LawrenceK/webbrick/Documentation/WebBrickQuickStart.tex

\documentclass[a4paper,12pt]{article}

\title{\sf{WebBrick}\linebreak Quick Start Guide}

%\lhead{\small{WebBrick Version 6.2 Quick Start Guide}}

\include{Version}

\include{QuickStart}

\printindex

\end{document}
