LawrenceK/webbrick/Documentation/Webrick.tex

\documentclass[a4paper,12pt]{article}

\title{\sf{WebBrick}\linebreak User and Reference Manual}

\include{Version}

\include{Overview}

\include{Architecture}

\include{WebInterface}

\include{Commands}

\include{IoBoard}

\include{Xml}

\include{IPSetting}

\include{UDPDefs}

\include{PythonSection}

\include{PHPSection}

\include{Applications}

\include{OutsideWorld}

\include{TempSensors}

\include{PowerRequirements}

\include{Revision}

\include{CEMarking}

\include{Gotchas}

\printindex

\end{document}
