LawrenceK/webbrick/Hardware/SwitchPlates/HVACIsolationSwitch.odt

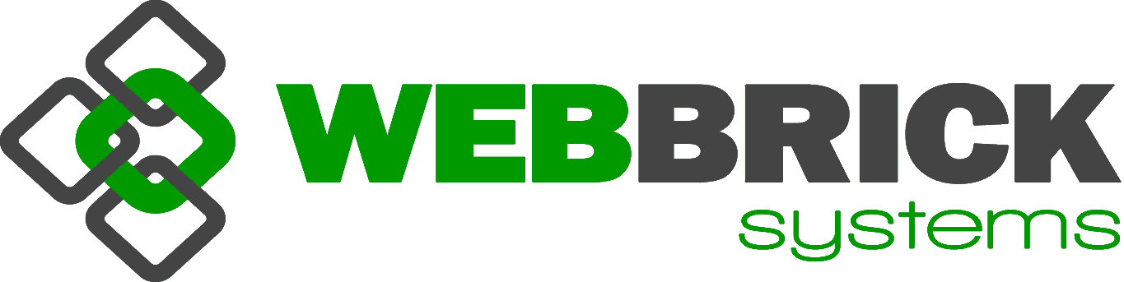
[picture p30: figure]

HVAC Isolation Switch

Andy Harris, 30th March 2008

# Introduction

There is a need to produce a switch that meets the following basic requirements:

- Local double pole isolation: To meet regulations (both 17th and 16th have this requirement)
- Auto/On/Off: So that local service technicians can be sure of the state of a device. For example, the boiler may be powered up and the technician needs to be certain that it has demand.

# Corollary Requirements

These follow on from the basic requirements:

- If the device is isolated, the Gateway needs to know this. For example if the device was a solar pump then the gateway could mark this as unavailable and therefore work around it with another heat source. (Meets the tenant: Missing is not broken).
- If the device is in Manual-On this should be shown on the UI. For heating devices there should be a sacrificial circuit somewhere to dissipate the heat. The Gateway should take no action that could confuse the service technician.
- If the device is in Manual-Off this should be shown on the UI. The Gateway may close any valves to bypass the device and mark it as unavailable.

# Electrical Requirements

Obviously HVAC plant is available in a wide range of capacities and therefore electrical demand. This will affect the rating of the isolation switch.

The demand routing scheme (switch/relay/etc) should not need more than 1A@230V capacity.

The signals provided back to the WebBrick (and thus onto the Gateway) should be 2KV isolated from the mains supply.

# CE Marking

Since the components should be simple off the shelf items and there are no processor chips, self certification by design file will be sufficient.
