LawrenceK/webbrick/Hardware/SwitchPlates/RequirementsSwitchBus.odt

# SwitchBus

13th March 2008, Version 0.9 Draft

# The need

Having delivered on the goal of affordable home automation. We now need to make out solution more widely deployable by making it easier and quicker to install.

Currently our switch plates need many connections that need to be understood in the context of the room for which they are installed (i.e. Is this a major or minor room, what DI and Mimics are being used).

We should also reduce the cable requirements to one CAT5 (CATn) per position. This alone would reduce the cost and time taken to install our solution as well as reduce the issues in finding cable runs.

One run per position would also reduce the patching needs at the star point, which again reduces space.

# The Requirements

There are a number of resource constraints that we have. Therefore the following need to be thought about:

- The need to maintain the current operation of the WebBrick in terms of Digital Inputs and Mimics.
- The need to minimise the impact on the WebBrick code base
- Impact on processor performance
- The configuration process of the Switch Plate and the WebBrick
- Available standards
- Cost
- The installation process, and minimise the changes to the training courses
- Building regulations (this means shallow back boxes and IP67 ratings in some application)
- Customer choice at the decorative level
- Future availability of web based panels

# The proposals

To meet the above, the following are suggested:

The PCB connects to the cable using an RJ45 plug and socket. In this way cables can be tested using regular data network test tools.

We create a PCB that implements SwitchBus on a 4 wire basis, where at least 0V and 5V are available. This would mean that if a 'web plate' was installed in the future, the charging requirements would already be met.

The PCB is engineered for the switches that we sell, but connections are available to any other type of switch.

The PCB and SwitchBus protocol could accommodate a temperature sensor. This sensor, when discovered would follow the same rules as the existing sensors.

The PCB, or its versions should cope with 1-4 push buttons and mimics. With options for rotary encoders.

The PCB and protocol should cope with an optional IR receiver.

The SwitchBus scheme should allow for both star and bus style wiring. Where space is at a premium a single cable could be taken to a room and then daisy chained around the relevant points.

The Switches should be configured via the WebBrick. The application can reside on the gateway.

The Switches and Mimics are to be mapped to existing digital inputs and mimics on the WebBrick.

Any provision for mapping a switch on one WebBrick to an action on another should be done through the gateway.

Response times should be better than debounce+10ms

# Looking forward

The same PCB technology to be laid out to take TACT style micro-switches and LEDs for mimics. In this way any number of caps could be used to create a wider range of plates.
