LawrenceK/webbrick/Hardware/SwitchPlates/SwitchMarshalling.odt

Quick capture of idea based on seeing the RJ45 connected switch plate.

Introduction

Much time is spent by our installers patching from the Gigabix frame to the WebBricks. We know from experience that every mistake weakens the integrity of the Gigabix frame and after about 5 punch downs one can no longer trust that section of the frame. We have spend tens of days debugging and tracking faults on Gigabix panels.

We also know that end to end testing of CATx cables is trivial when they are terminated with RJ45 plugs at both ends, and they can have warranties placed on them.

Therefore this idea is about replacing the Gigabix panel with a simple product or our own for:

Switch Plates

Temperature Sensors

This could expand to other functions but these are the most pressing.

Scenario

Most rooms rooms have two switch plates, most plates are two buttons,

Some rooms have up to four switch plates, these are typically the large rooms or hallways with multiple entry/exit routes.

Proposal

We design two PCBs as a long strips of mounted RJ45 sockets where:

The first PCB is optimised for switch plates:

- RJ45s are hard wired as pairs+1 (because most rooms have two plates)
- DIL Jumpers can be used to connect pairs into quads
- The grounds are commoned together
- The +1 RJ45 is the connection to the WebBrick and can therefore have a standard colour scheme to reduce confusion and connection numbers

The second PCB is optimised for Temperature sensors:

- RJ45s are wired in pairs+1RJ11 with the loop through to ensure the correct buss arrangement for temperature sensors.
- DIL jumpers can connect pairs into quads (not into 5 to reduce length issues overall)
- The RJ11 is the connection to the WebBrick, again with a standard colour scheme

Think how this would speed up an installation !!

Thinking further

If we plan ahead. This board layout may well be able to support Schuster Bus, if not, an active version of the board in the same form factor would.
