LawrenceK/webbrick/Hardware/8SSR/Docs/8SSR(2)-1AS.pptx

GG

1 2 3 4 5 6 7 8 C PE
Contacts

WebBrick 8SSR Driver™
WE 08 - 120

Inputs
1 2 3 4 5 6 7 8 G G G G

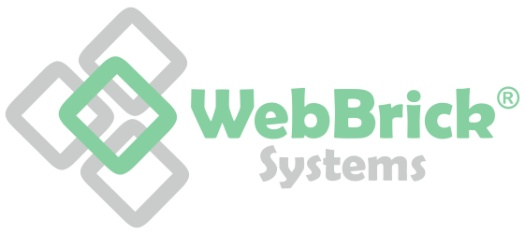
[picture p32: figure]

INSTALLER
