LawrenceK/webbrick/Hardware/WebBrick/6.0/Enclosure and Top Artwork/Enclosure.pdf

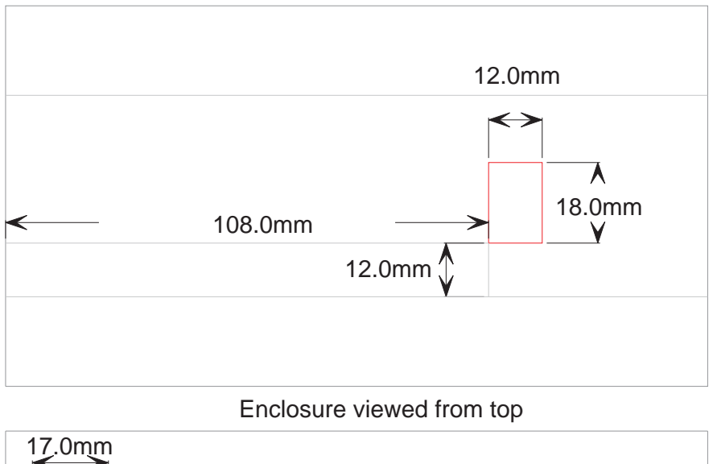
[picture p34: figure]
Enclosure viewed from top
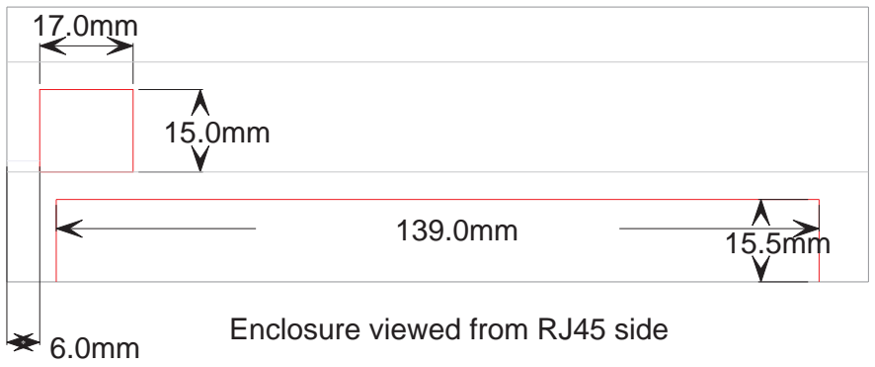
[picture p35: figure]
Enclosure viewed from RJ45 side

139.0mm

Enclosure viewed from 'plain' side

15.5mm
