LawrenceK/webbrick/Documentation/CETesting/CETests.pdf

WebBrick 6-64 test results

# WebBrick 6-64, Model WB10B60 Internal Testing results Version 1.03

### Andy Harris

### November 21, 2005

November 2005 Document Version 1.01 - Initial Version

WebBrick Software Versions 6.0

c O2M8 Ltd | 1 | www.o2m8.com

WebBrick 6-64 test results | CONTENTS

## Contents

1 Introduction | 3
2 General Ratings | 3
3 Full Mains Load Testing | 4
c O2M8 Ltd | 2 | www.o2m8.com

WebBrick 6-64 test results

## 1 Introduction

The WebBrick is effectivily a web enabled programmable logic controller that is designed to control and monitor various elements of home automation.

Logically and physically it is divided into 3 main components:

- WebServer This component provides a HTTP and UDP interface to the network via a standard RJ45 socket
- Processor board This component holds the main processor and oscillator along with a switching step down supply and various signal conditioning components.
- IO board This component is split into two sections, the first provides a base for the processor board and all the attendant low voltage and intrinsically safe connections. The section section handles domestic mains via 4 zero volt switching Triac circuits and two relays.

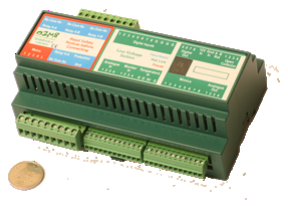
[picture p42: figure]

## 2 General Ratings

The WebBrick has a full range of connections and operating parameters, those relating to safety are given here:

- Digital Inputs These present 5V DC via weak pull-ups of 4.7K. Inputs are protected by a CR network of 330R and 1uf. Digital Inputs are triggered by pulling to ground. Maximum current feed is 5mA.
c O2M8 Ltd | 3 | www.o2m8.com

WebBrick 6-64 test results

- Analogue Inputs These are high impedance 1M inputs which can accept a 0-5V DC signal.
- Dallas 1 Input This provides three connections:

– 5V output directly from the switch down power supply maximum current feed is a possible 350mA.

– Data connection, pulled to 5V via 1K, maxium current feed is 5mA

– Ground return

- Digital Outputs These present a 5V DC signal when in the ’On’ state, maximum current feed available is 20mA.
- Open Collector Outputs These provide a pull to ground output with a maximum sink capacity of 500mA per channel.
- Analogue Outputs These provide a 0-10V DC signal with a maximum current feed of 50mA per channel
- Mains outputs These provide 4 mains 240VAC outputs each rated at 4A with an overall capacity of 6.3A aggregated over the 4 outputs.
- Dry Relay Contacts Two double pole changeover relays rated a 4A are provided. The tracks for these come within 3mm of the tracks used in the Triac circuits.
- Mains Protective Ground This provides a safety barrier around the relays and triac drivers and should be connected if the WebBrick is used in a mains driven application.

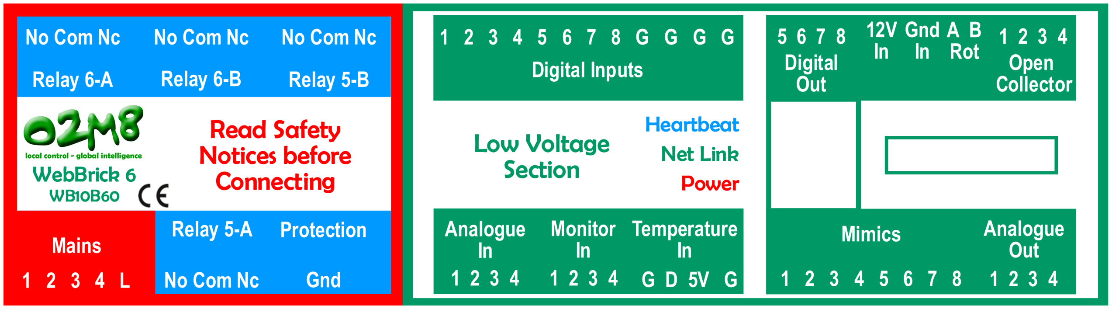
[picture p43: figure]

## 3 Full Mains Load Testing

Two WebBricks were tested at full rated load of 6.3A over three outputs. The load was provided by 3off 500W halogen lamps. Testing was conducted in an ambient temperature of 21 Deg C to 26 Deg C with a test duration of 2 hours per test.

c O2M8 Ltd | 4 | www.o2m8.com

WebBrick 6-64 test results | 3.1 Bare board test

### 3.1 Bare board test

The WebBricks were tested with the enclosures removed.

### 3.1.1 Results

After two hours the heatsink reached a temperature of 79 Deg C

### 3.2 Full product test Horizontal

### 3.2.1 Results

After two hours the heatsink reached a temperature of 104.1 Deg C. An additional load of 500W was added making the total load 2kW. The Heatshink rose to 105 Deg C and the internal fuse blew within 30 seconds.

### 3.3 Full product test Vertical

### 3.3.1 Results

After three hours the heatsink reached a temperature of 81 Deg C. An additional load of 500W was added making the total load 2kW. The internal fuse blew within 30 seconds.

c O2M8 Ltd | 5 | www.o2m8.com
