LawrenceK/webbrick/Documentation/InfraRedEmitterDataSheet.tex

\documentclass[a4paper,12pt]{article}
\usepackage{graphicx, float, fancyheadings, a4wide, makeidx, verbatim,avant,helvet}
\usepackage{}
\pagestyle{fancyplain}
\setlength{\parindent}{0pt}
\setlength{\parskip}{6pt}

\newcommand{\param}[1] {\textless{}#1\textgreater{}}

\title{\sf{Datasheet for Infra Red Receiver}}
\lfoot{\tiny{\copyright L.P.Klyne}}

\author{Andy Harris}

\makeindex

\begin{document}

\maketitle

\begin{figure}[H]
\centering

\end{figure}

\begin{figure}[H]
\centering

\end{figure}

\begin{description}
\item[Feb 2007 Document Version 1.00]
\end{description}

\begin{description}
\item[http:\\www.webbricksystems.com] for company information
\item[http:\\www.webbrick.co.uk] for webbrick information
\end{description}

\pagebreak

\include{InfraRedEmitter}

\end{document}
