LawrenceK/webbrick/Hardware/Isolator/Docs/Label.pptx

1 2 3 4 5 6 7 8 C PE
Contacts

GG

WebBrick Isolator™ WI 08-02


INSTALLER
