LawrenceK/webbrick/Documentation/CETesting/O2M8_berl.png

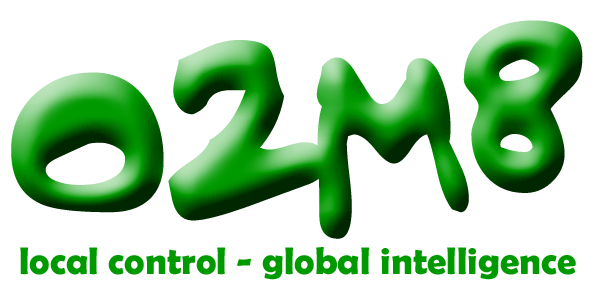
Documentation/CETesting/O2M8_berl.png
