LawrenceK/webbrick/Documentation/Harmony/After.jpg

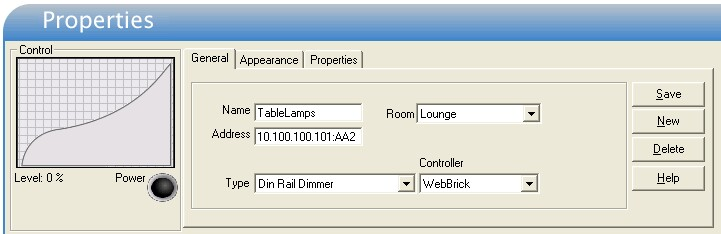
Documentation/Harmony/After.jpg
