LawrenceK/webbrick/Documentation/Harmony/Architecture.png

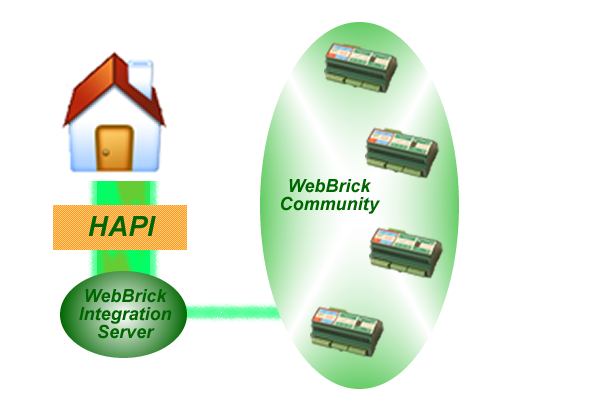
Documentation/Harmony/Architecture.png
