LawrenceK/webbrick/Documentation/Harmony/Device.jpg

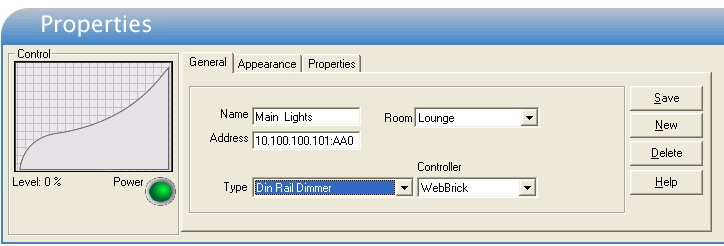
Documentation/Harmony/Device.jpg
