LawrenceK/webbrick/Documentation/Harmony/Initial.jpg

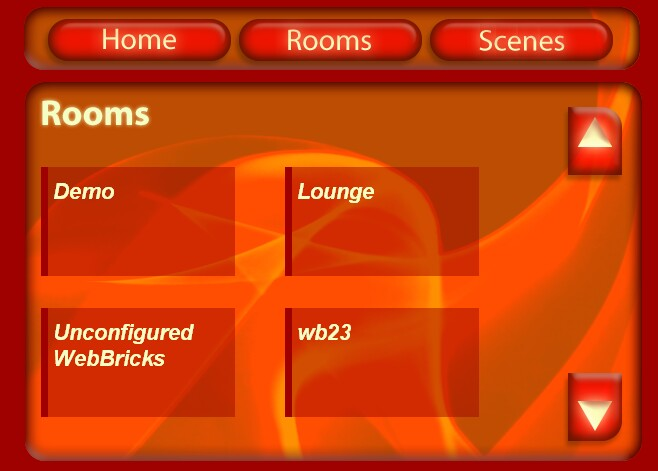
Documentation/Harmony/Initial.jpg
