LawrenceK/webbrick/Documentation/Harmony/Lounge.jpg

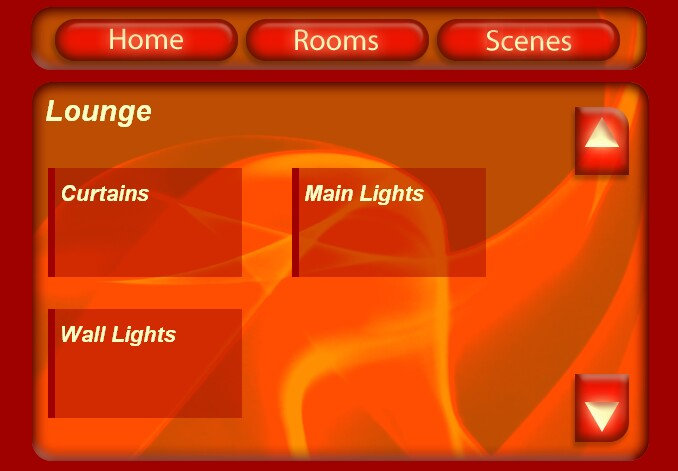
Documentation/Harmony/Lounge.jpg
