LawrenceK/webbrick/Documentation/Harmony/MainLights.jpg

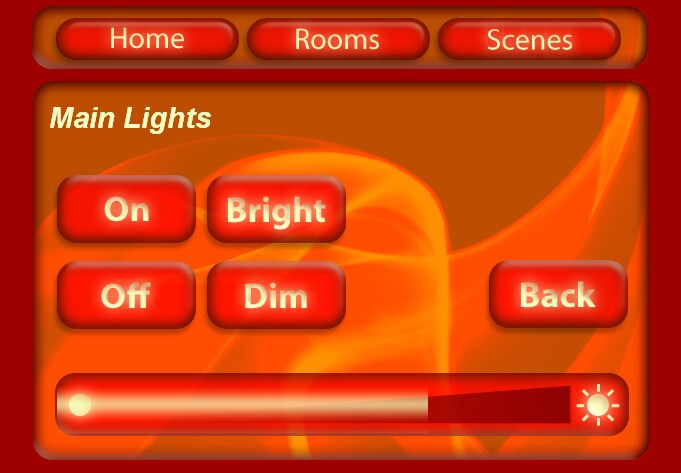
Documentation/Harmony/MainLights.jpg
