LawrenceK/webbrick/Documentation/Harmony/NewZones.jpg

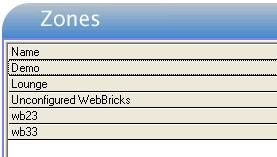
Documentation/Harmony/NewZones.jpg
