LawrenceK/webbrick/Documentation/Harmony/wb23.jpg

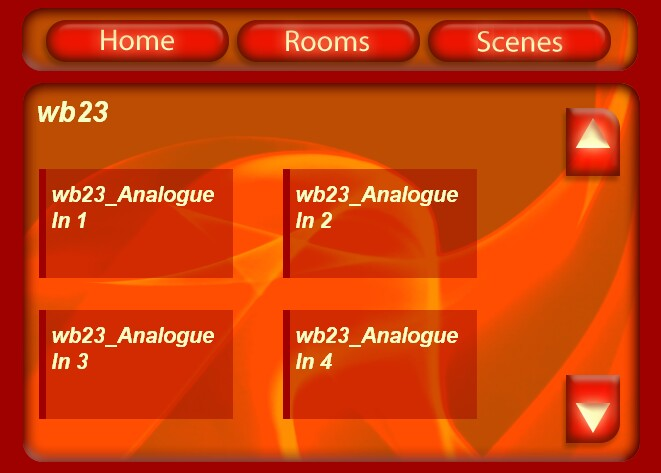
Documentation/Harmony/wb23.jpg
