LawrenceK/webbrick/Documentation/Harmony/wbView.jpg

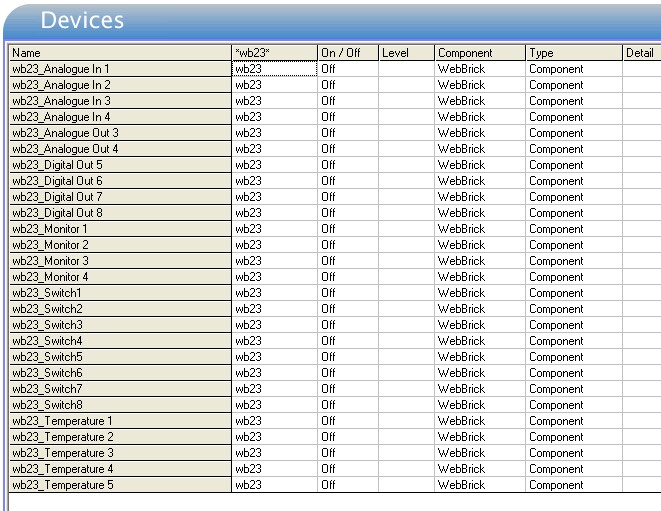
Documentation/Harmony/wbView.jpg
