LawrenceK/webbrick/Documentation/Images/CCSrc.jpg

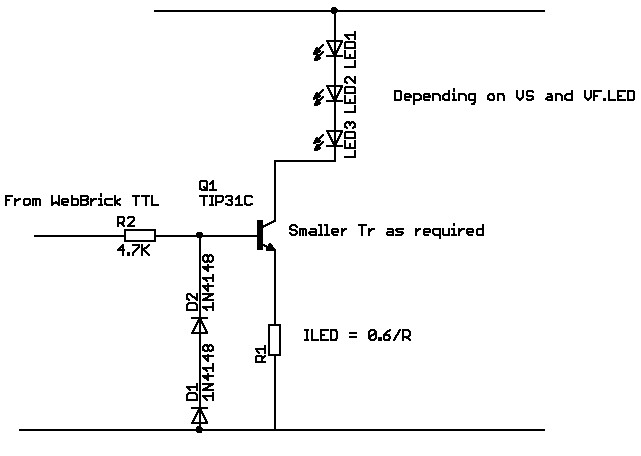
Documentation/Images/CCSrc.jpg
