LawrenceK/webbrick/Documentation/Images/PIRConnection.png

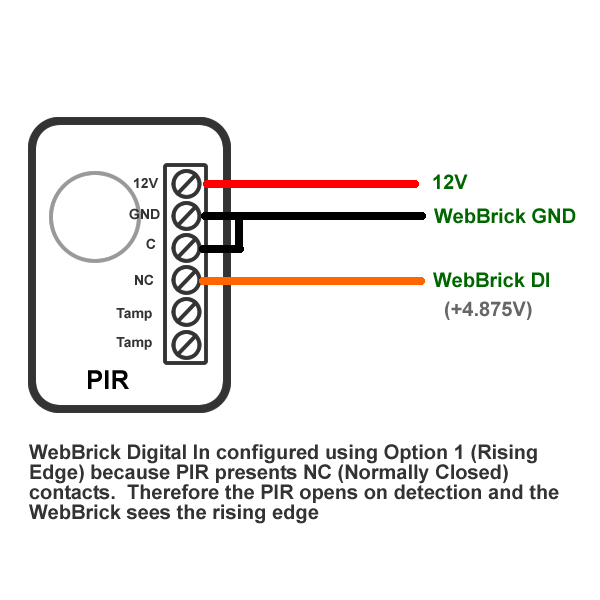
Documentation/Images/PIRConnection.png
