LawrenceK/webbrick/Documentation/Images/RotaryEncoderConnections.png

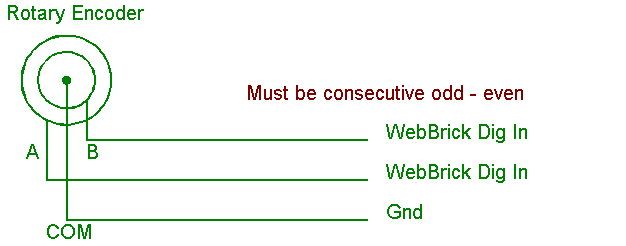
Documentation/Images/RotaryEncoderConnections.png
