LawrenceK/webbrick/Documentation/Images/SilentGliss.jpg

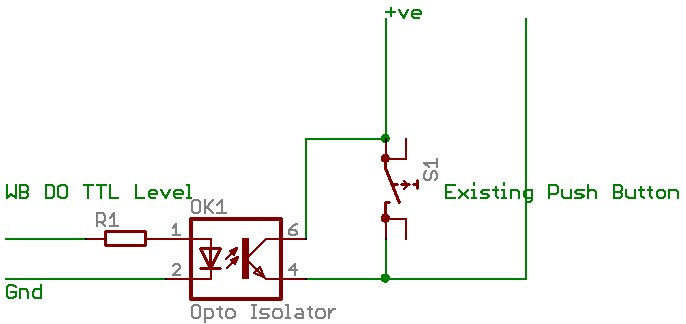
Documentation/Images/SilentGliss.jpg
