LawrenceK/webbrick/Documentation/Images/SSR.png

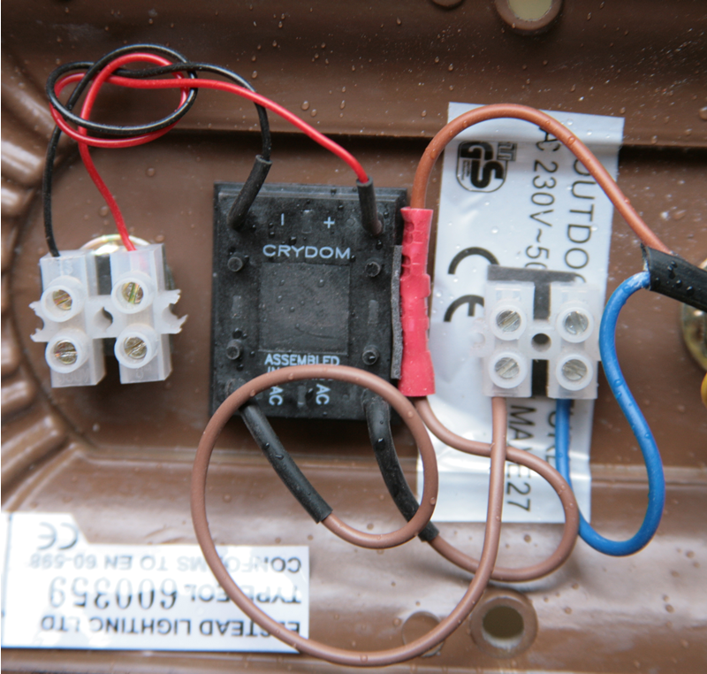
Documentation/Images/SSR.png
