LawrenceK/webbrick/Documentation/Images/TempSensorConnections.png

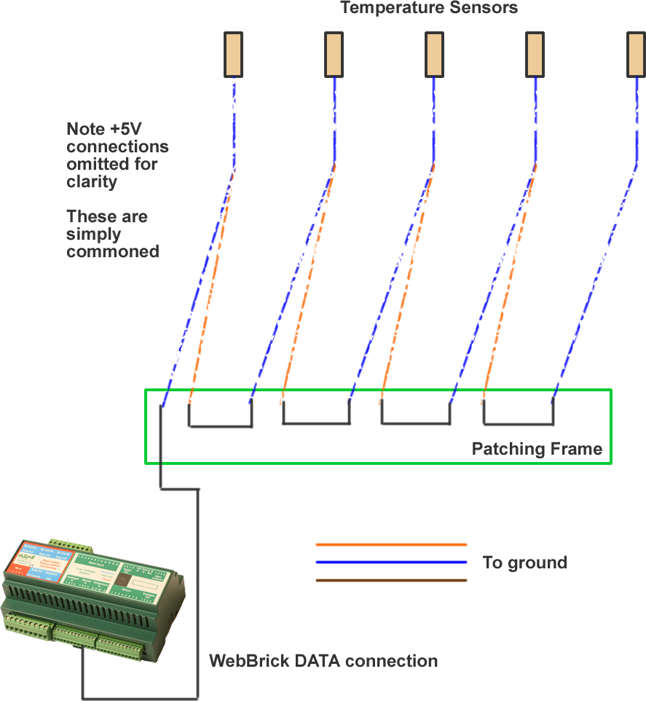
Documentation/Images/TempSensorConnections.png
