LawrenceK/webbrick/Documentation/Images/WbMon.jpg

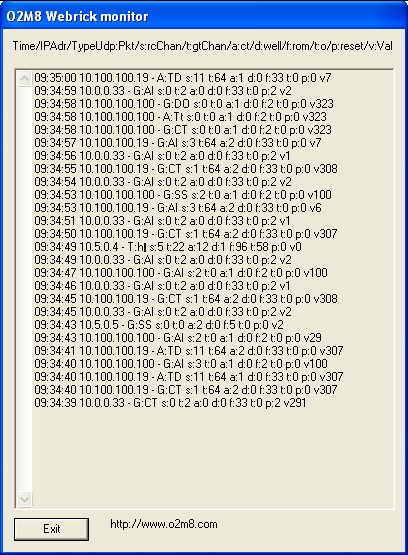
Documentation/Images/WbMon.jpg
