LawrenceK/webbrick/Documentation/PackShots/SidePackShot.png

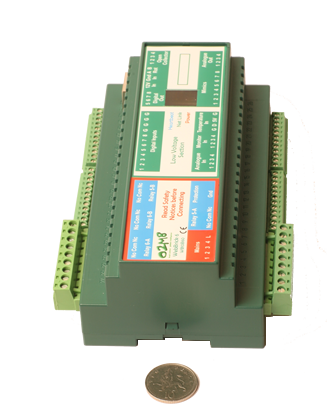
Documentation/PackShots/SidePackShot.png
