LawrenceK/webbrick/Documentation/PackShots/TopPackShot.png

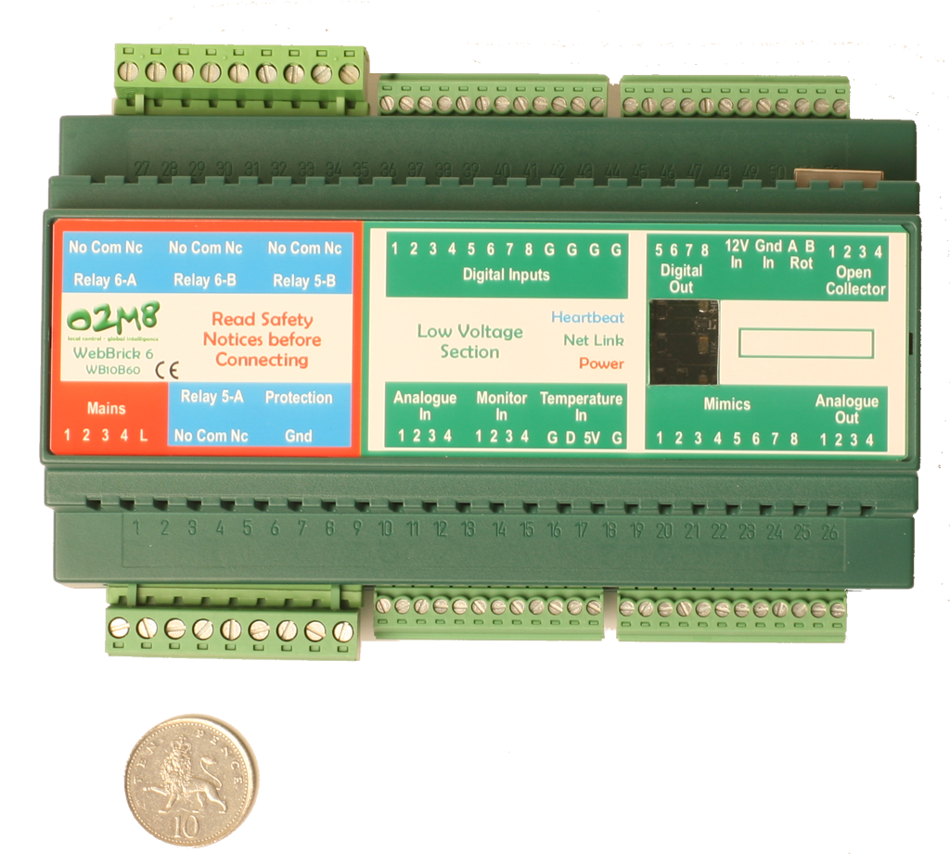
Documentation/PackShots/TopPackShot.png
