LawrenceK/webbrick/Hardware/RoomController/roomPlate2.jpg

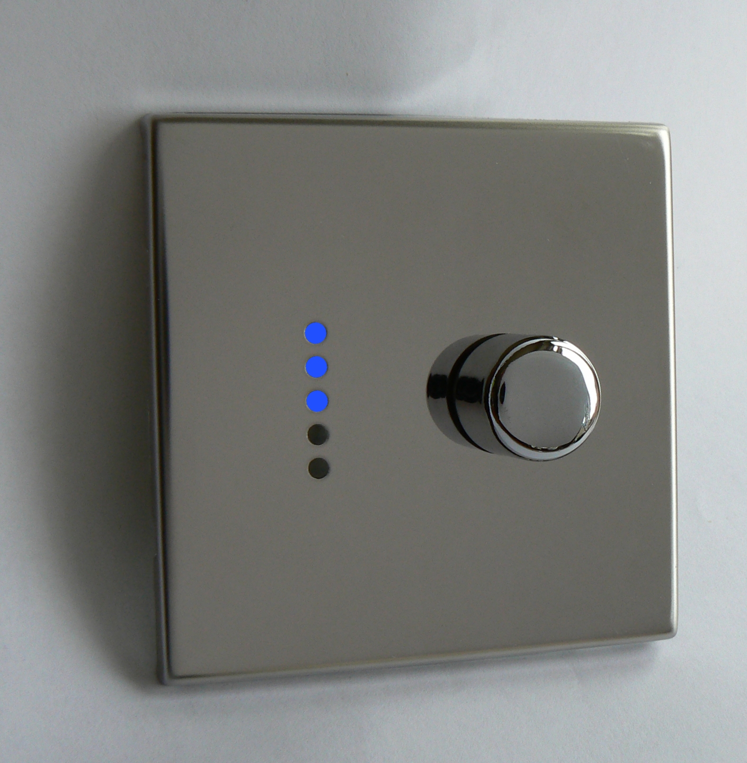
Hardware/RoomController/roomPlate2.jpg
