LawrenceK/webbrick/Hardware/SwitchPlates/Hamilton.png

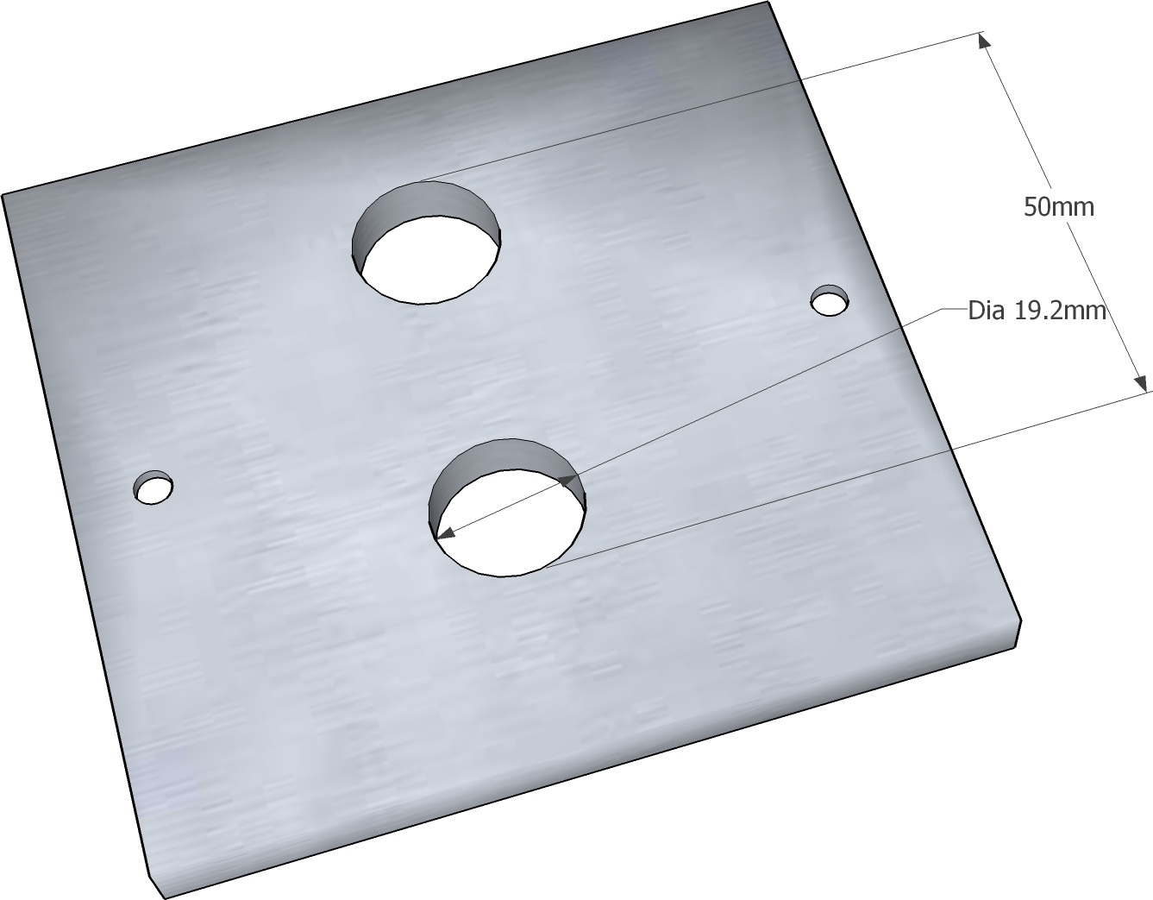
Hardware/SwitchPlates/Hamilton.png
