LawrenceK/webbrick/Hardware/SwitchPlates/HamiltonSingle.png

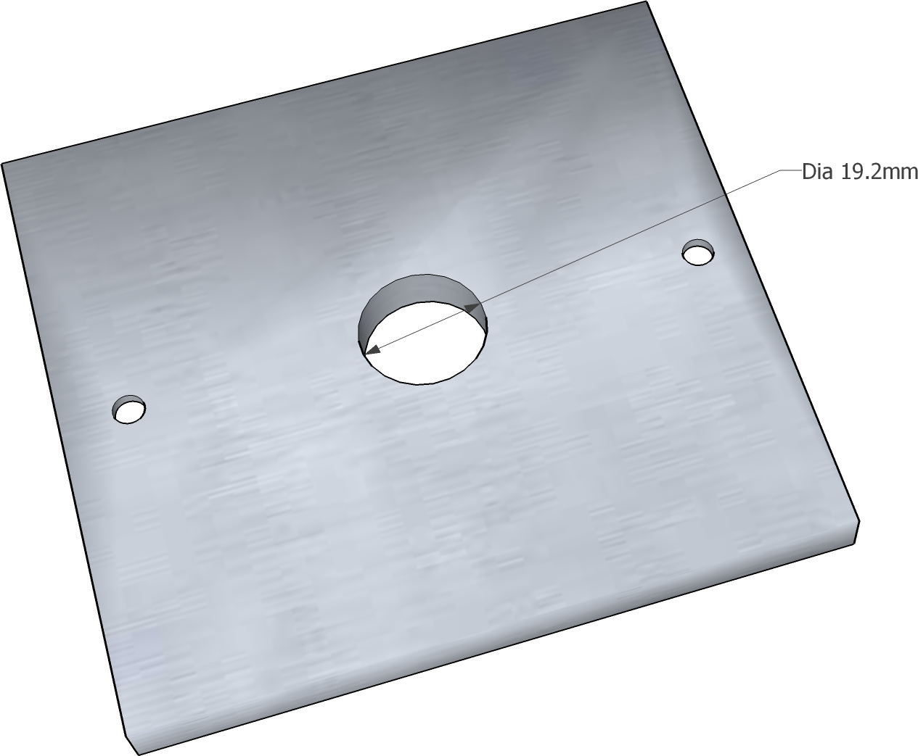
Hardware/SwitchPlates/HamiltonSingle.png
