LawrenceK/webbrick/Hardware/SwitchPlates/TouchSwitch/RoughSketchSide.png

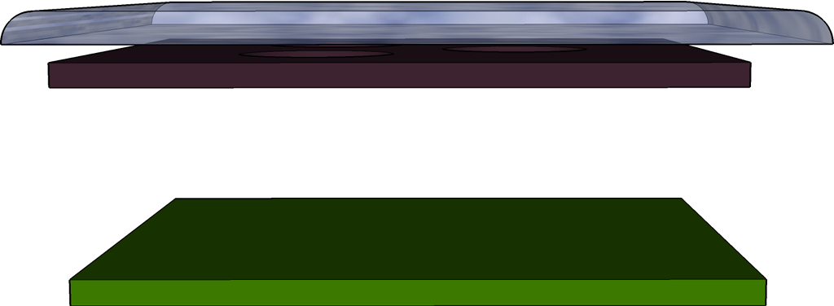
Hardware/SwitchPlates/TouchSwitch/RoughSketchSide.png
