LawrenceK/webbrick/Hardware/SwitchPlates/TouchSwitch/RoughSketchTop.png

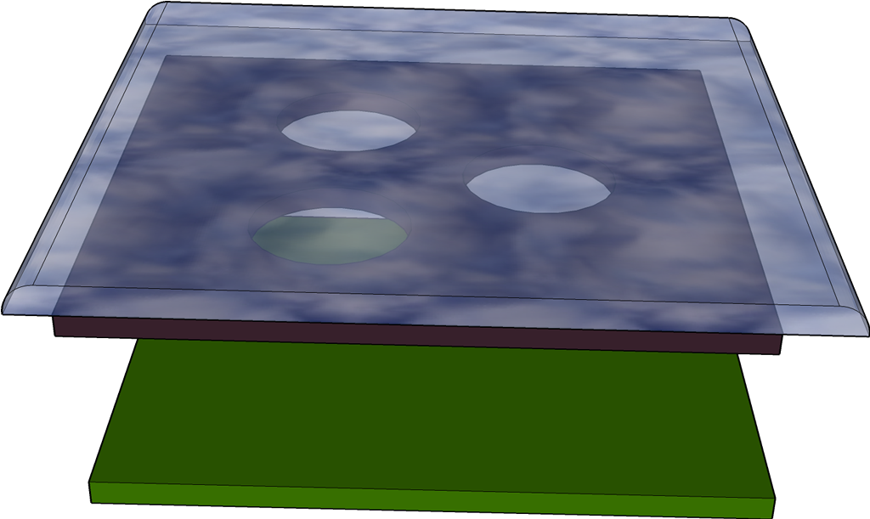
Hardware/SwitchPlates/TouchSwitch/RoughSketchTop.png
