LawrenceK/webbrick/Hardware/Webbrick Interfaces/Example CCT Diagrams/Inputs/Velux.bmp

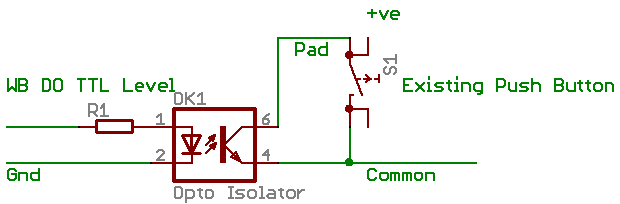
Hardware/Webbrick Interfaces/Example CCT Diagrams/Inputs/Velux.bmp
