LawrenceK/webbrick/Hardware/Webbrick Interfaces/Example CCT Diagrams/Outputs/CrudeLED.png

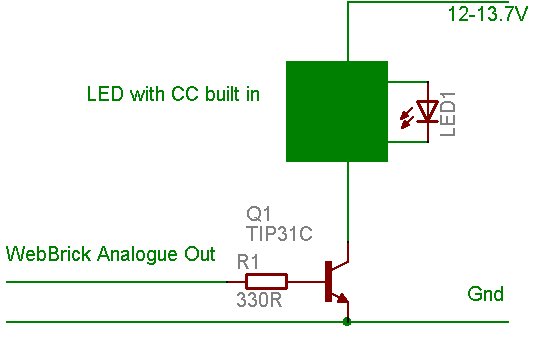
Hardware/Webbrick Interfaces/Example CCT Diagrams/Outputs/CrudeLED.png
