LawrenceK/webbrick/Hardware/Webbrick Interfaces/SecurityPIRS/PIRConnections.png

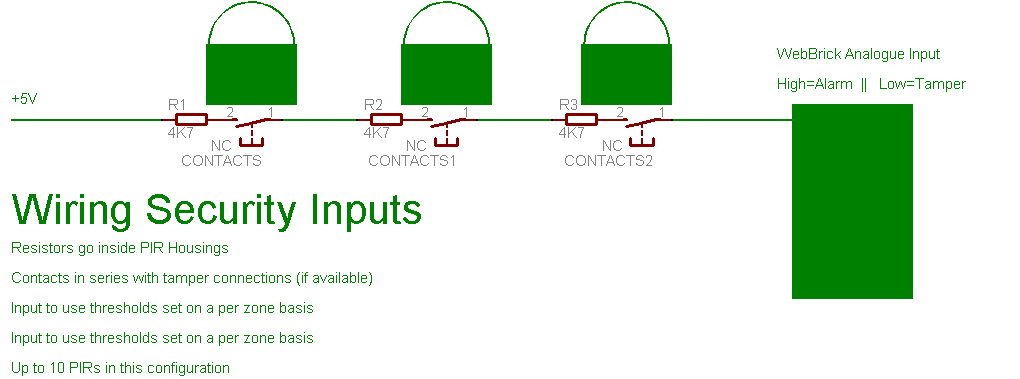
Hardware/Webbrick Interfaces/SecurityPIRS/PIRConnections.png
