LawrenceK/webbrick/Hardware/WebBrick/6.0/Enclosure and Top Artwork/6.4Enclosure.png

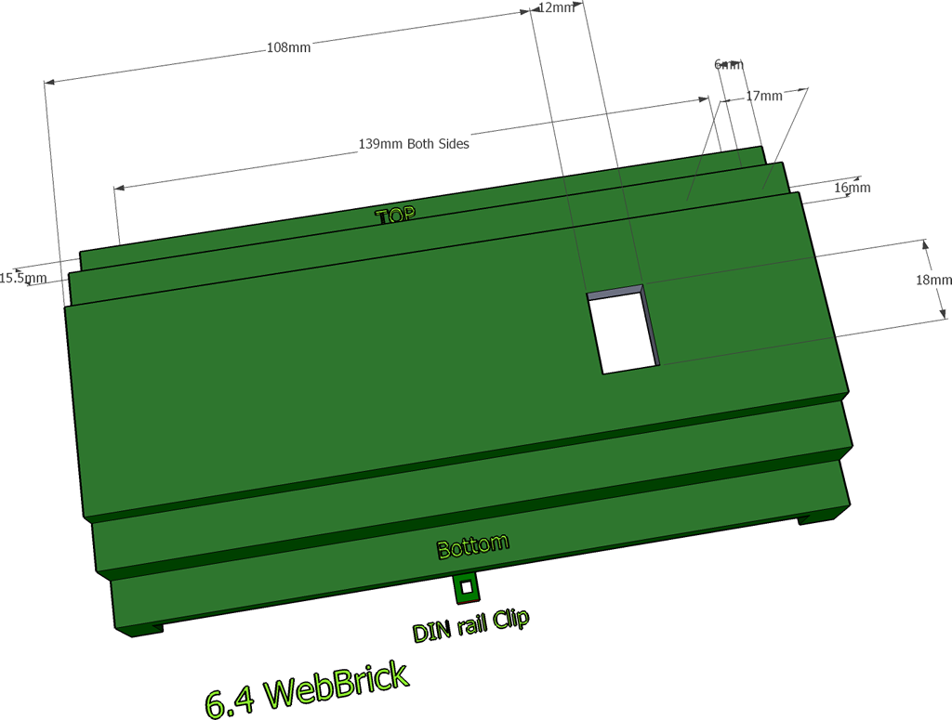
Hardware/WebBrick/6.0/Enclosure and Top Artwork/6.4Enclosure.png
