LawrenceK/webbrick/Hardware/WebBrick/6.0/Enclosure and Top Artwork/Enclosure.png

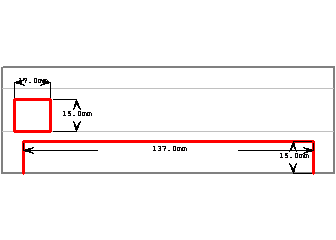
Hardware/WebBrick/6.0/Enclosure and Top Artwork/Enclosure.png
