LawrenceK/webbrick/Hardware/WebBrick/PulseTransformerConnections.jpg

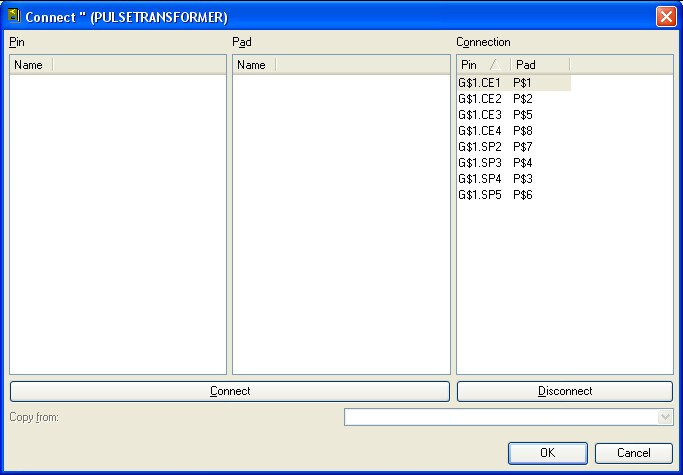
Hardware/WebBrick/PulseTransformerConnections.jpg
