LawrenceK/webbrick/Documentation/CETesting/T1804_rad_051208.pdf

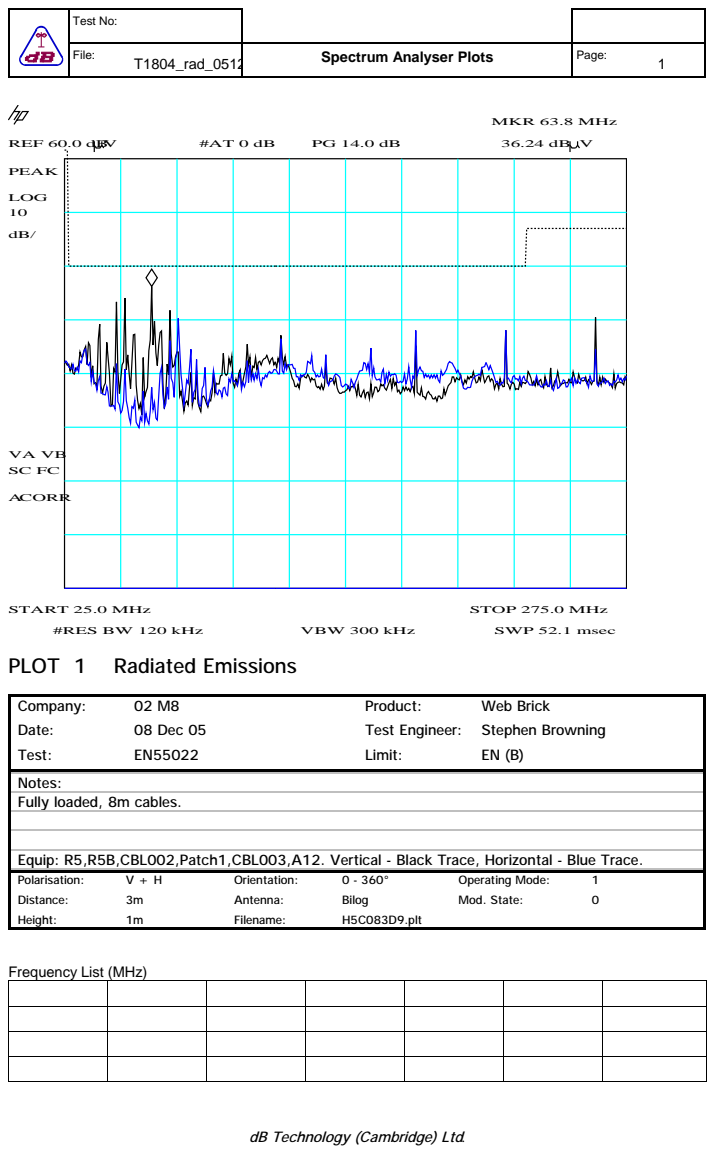
[picture p103: page 1]
#RES BW 120 kHz; VBW 300 kHz; SWP 52.1 msec; REF 60.0 dBV; LOG 10; START 25.0 MHz; STOP 275.0 MHz; MKR 63.8 MHz; PEAK; ACORR; Test:; Limit:; Date:; 08 Dec 05; Test Engineer: Stephen Browning; Company:; Product:; Web Brick; Height:; Filename:; H5C083D9.plt; Distance:; Antenna:; Bilog; Mod. State:; Polarisation:; Orientation:; Operating Mode:

Test No:

File: | Spectrum Analyser Plots | Page: T1804_rad_051208.l

PLOT 1 Radiated Emissions

Notes:
Fully loaded, 8m cables.

Equip: R5,R5B,CBL002,Patch1,CBL003,A12. Vertical - Black Trace, Horizontal - Blue Trace.

Frequency List (MHz)

dB Technology (Cambridge) Ltd.

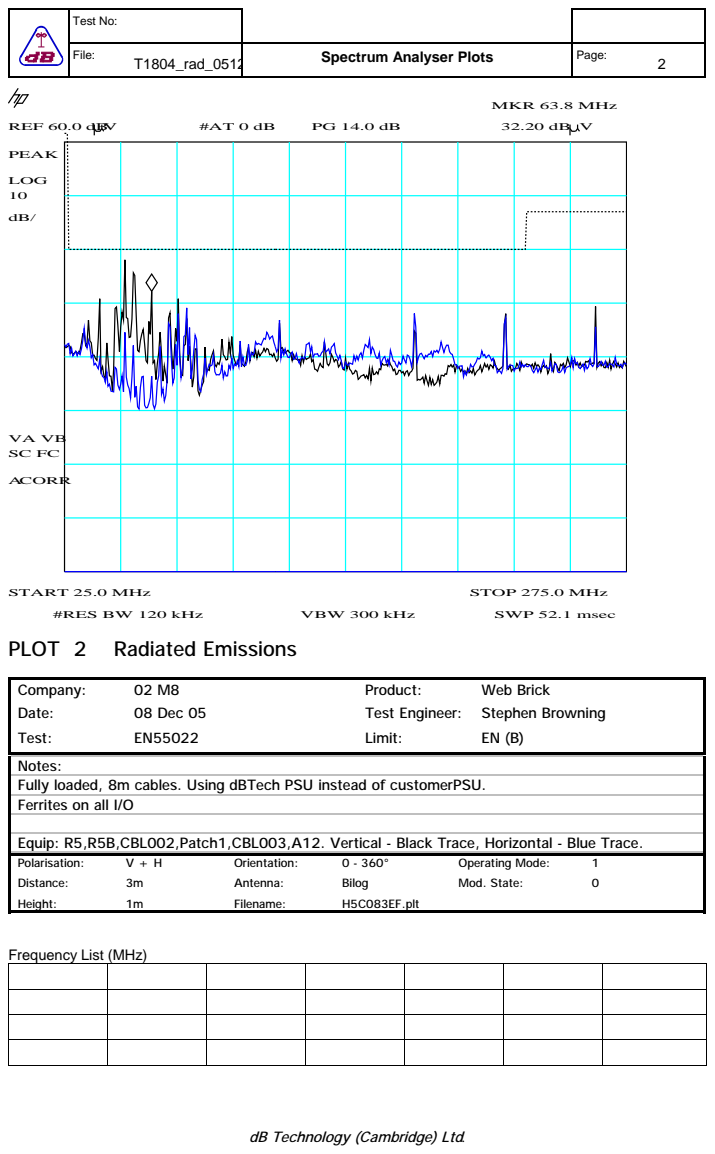
[picture p104: page 2]
#RES BW 120 kHz; VBW 300 kHz; SWP 52.1 msec; REF 60.0 dBV; LOG 10; START 25.0 MHz; STOP 275.0 MHz; MKR 63.8 MHz; PEAK; ACORR; Test:; Limit:; Date:; 08 Dec 05; Test Engineer: Stephen Browning; Company:; Product:; Web Brick; Height:; Filename:; H5C083EF.plt; Distance:; Antenna:; Bilog; Mod. State:; Polarisation:; Orientation:; Operating Mode:

PLOT 2 Radiated Emissions

Notes:
Fully loaded, 8m cables. Using dBTech PSU instead of customerPSU.
Ferrites on all I/O

Equip: R5,R5B,CBL002,Patch1,CBL003,A12. Vertical - Black Trace, Horizontal - Blue Trace.

Frequency List (MHz)

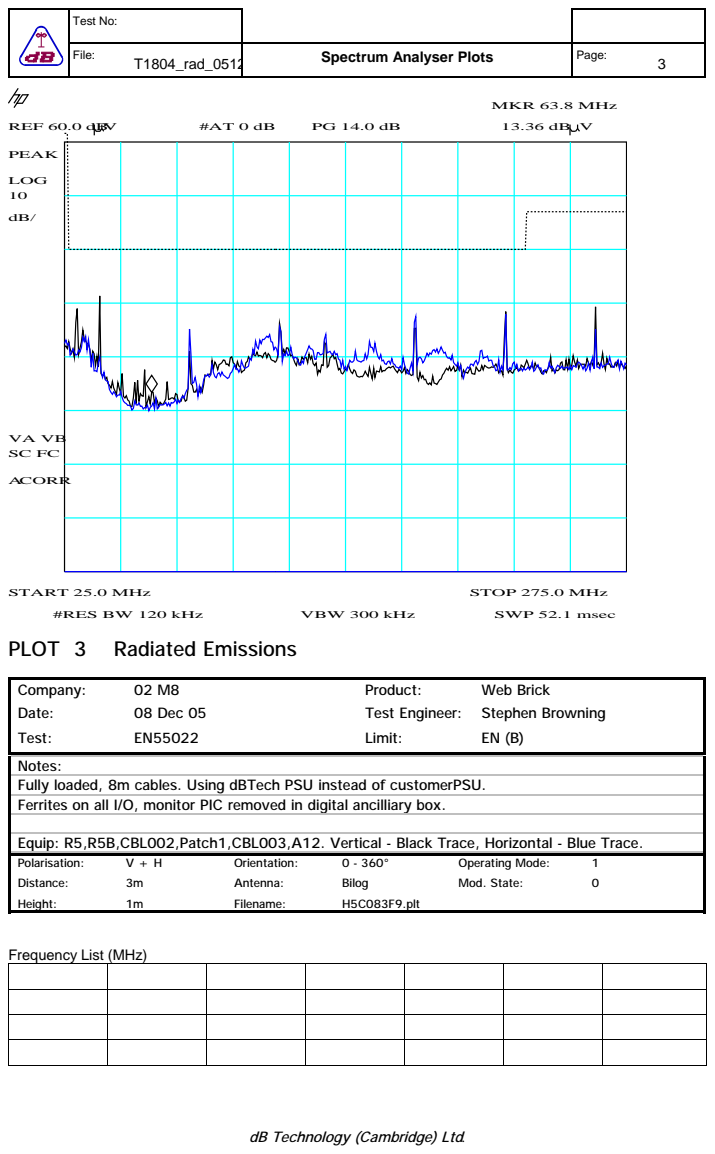
[picture p105: page 3]
#RES BW 120 kHz; VBW 300 kHz; SWP 52.1 msec; REF 60.0 dBV; LOG 10; START 25.0 MHz; STOP 275.0 MHz; MKR 63.8 MHz; PEAK; ACORR; Test:; Limit:; Date:; 08 Dec 05; Test Engineer: Stephen Browning; Company:; Product:; Web Brick; Height:; Filename:; H5C083F9.plt; Distance:; Antenna:; Bilog; Mod. State:; Polarisation:; Orientation:; Operating Mode:

PLOT 3 Radiated Emissions

Notes:
Fully loaded, 8m cables. Using dBTech PSU instead of customerPSU.
Ferrites on all I/O, monitor PIC removed in digital ancilliary box.

Equip: R5,R5B,CBL002,Patch1,CBL003,A12. Vertical - Black Trace, Horizontal - Blue Trace.

Frequency List (MHz)

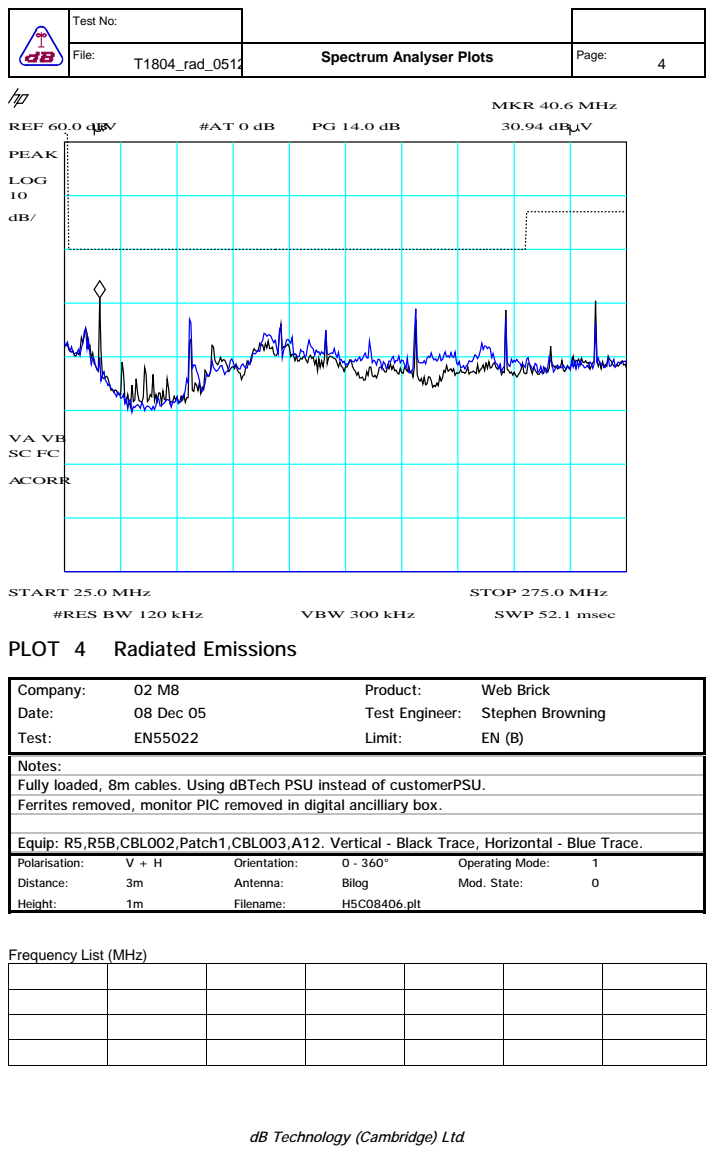
[picture p106: page 4]
#RES BW 120 kHz; VBW 300 kHz; SWP 52.1 msec; REF 60.0 dBV; LOG 10; START 25.0 MHz; STOP 275.0 MHz; MKR 40.6 MHz; PEAK; ACORR; Test:; Limit:; Date:; 08 Dec 05; Test Engineer: Stephen Browning; Company:; Product:; Web Brick; Height:; Filename:; H5C08406.plt; Distance:; Antenna:; Bilog; Mod. State:; Polarisation:; Orientation:; Operating Mode:

PLOT 4 Radiated Emissions

Notes:
Fully loaded, 8m cables. Using dBTech PSU instead of customerPSU.
Ferrites removed, monitor PIC removed in digital ancilliary box.

Equip: R5,R5B,CBL002,Patch1,CBL003,A12. Vertical - Black Trace, Horizontal - Blue Trace.

Frequency List (MHz)

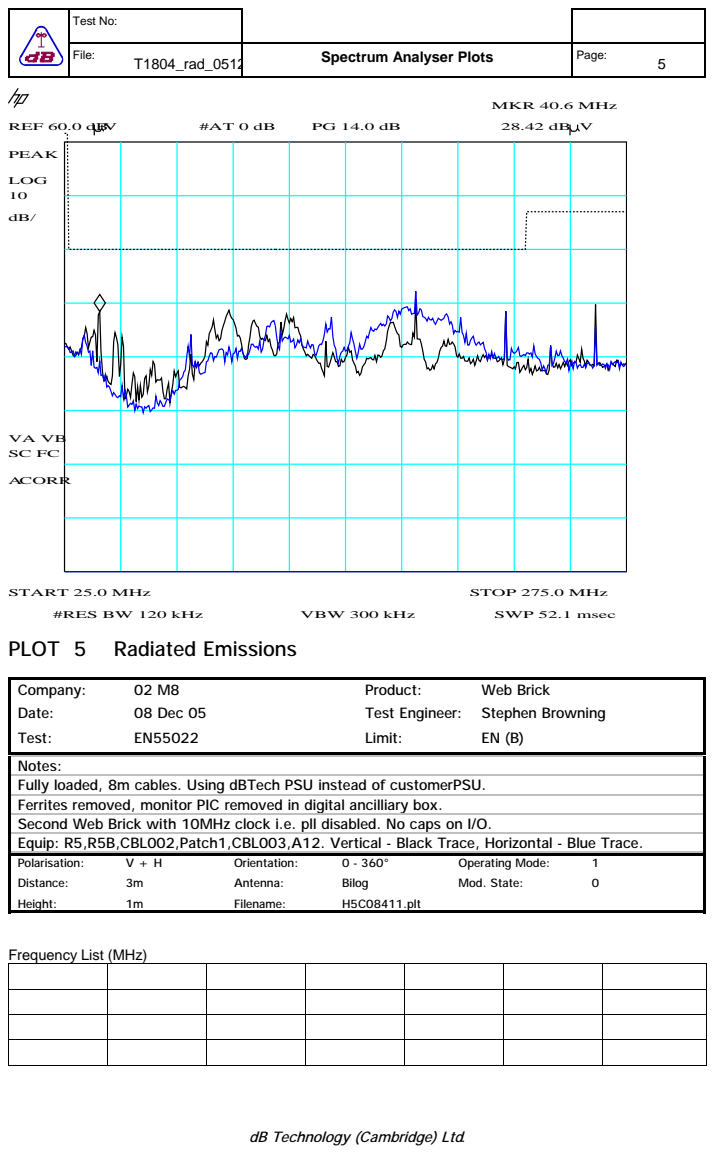
[picture p107: page 5]
#RES BW 120 kHz; VBW 300 kHz; SWP 52.1 msec; REF 60.0 dBV; LOG 10; START 25.0 MHz; STOP 275.0 MHz; MKR 40.6 MHz; PEAK; ACORR; Test:; Limit:; Date:; 08 Dec 05; Test Engineer: Stephen Browning; Company:; Product:; Web Brick; Height:; Filename:; H5C08411.plt; Distance:; Antenna:; Bilog; Mod. State:; Polarisation:; Orientation:; Operating Mode:

PLOT 5 Radiated Emissions

Notes:
Fully loaded, 8m cables. Using dBTech PSU instead of customerPSU.
Ferrites removed, monitor PIC removed in digital ancilliary box.
Second Web Brick with 10MHz clock i.e. pll disabled. No caps on I/O.
Equip: R5,R5B,CBL002,Patch1,CBL003,A12. Vertical - Black Trace, Horizontal - Blue Trace.

Frequency List (MHz)

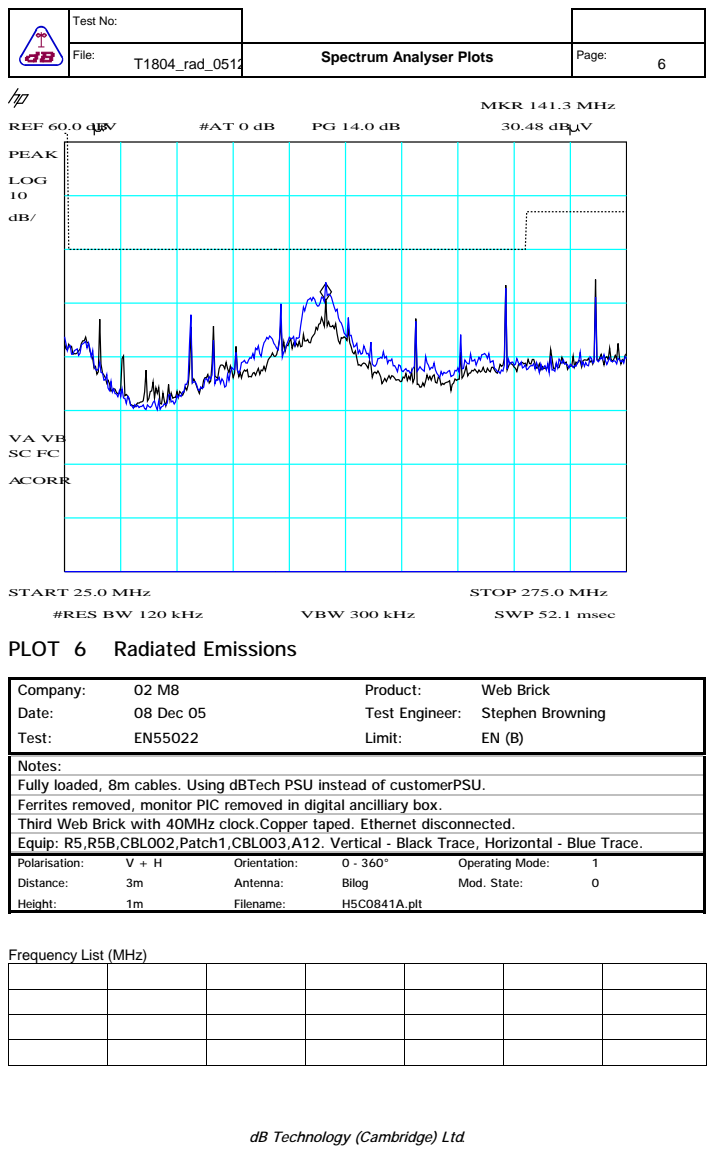
[picture p108: page 6]
#RES BW 120 kHz; VBW 300 kHz; SWP 52.1 msec; REF 60.0 dBV; LOG 10; START 25.0 MHz; STOP 275.0 MHz; MKR 141.3 MHz; PEAK; ACORR; Test:; Limit:; Date:; 08 Dec 05; Test Engineer: Stephen Browning; Company:; Product:; Web Brick; Height:; Filename:; H5C0841A.plt; Distance:; Antenna:; Bilog; Mod. State:; Polarisation:; Orientation:; Operating Mode:

PLOT 6 Radiated Emissions

Notes:
Fully loaded, 8m cables. Using dBTech PSU instead of customerPSU.
Ferrites removed, monitor PIC removed in digital ancilliary box.
Third Web Brick with 40MHz clock.Copper taped. Ethernet disconnected.
Equip: R5,R5B,CBL002,Patch1,CBL003,A12. Vertical - Black Trace, Horizontal - Blue Trace.

Frequency List (MHz)

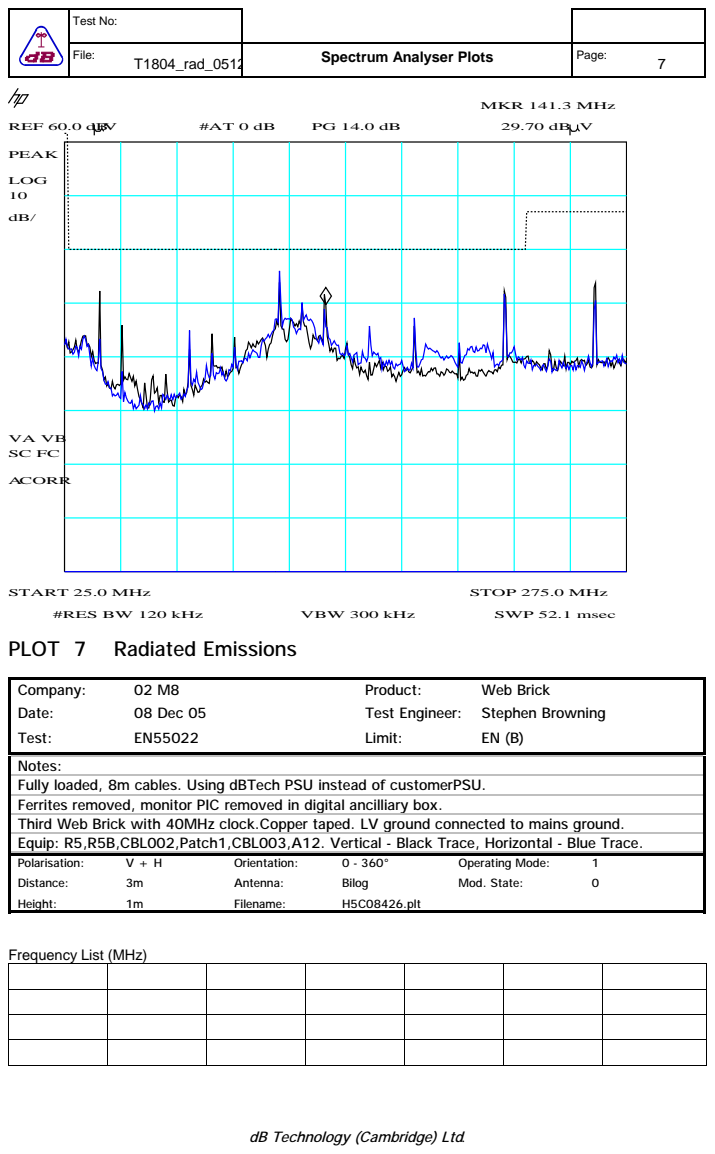
[picture p109: page 7]
#RES BW 120 kHz; VBW 300 kHz; SWP 52.1 msec; REF 60.0 dBV; LOG 10; START 25.0 MHz; STOP 275.0 MHz; MKR 141.3 MHz; PEAK; ACORR; Test:; Limit:; Date:; 08 Dec 05; Test Engineer: Stephen Browning; Company:; Product:; Web Brick; Height:; Filename:; H5C08426.plt; Distance:; Antenna:; Bilog; Mod. State:; Polarisation:; Orientation:; Operating Mode:

PLOT 7 Radiated Emissions

Notes:
Fully loaded, 8m cables. Using dBTech PSU instead of customerPSU.
Ferrites removed, monitor PIC removed in digital ancilliary box.
Third Web Brick with 40MHz clock.Copper taped. LV ground connected to mains ground.
Equip: R5,R5B,CBL002,Patch1,CBL003,A12. Vertical - Black Trace, Horizontal - Blue Trace.

Frequency List (MHz)

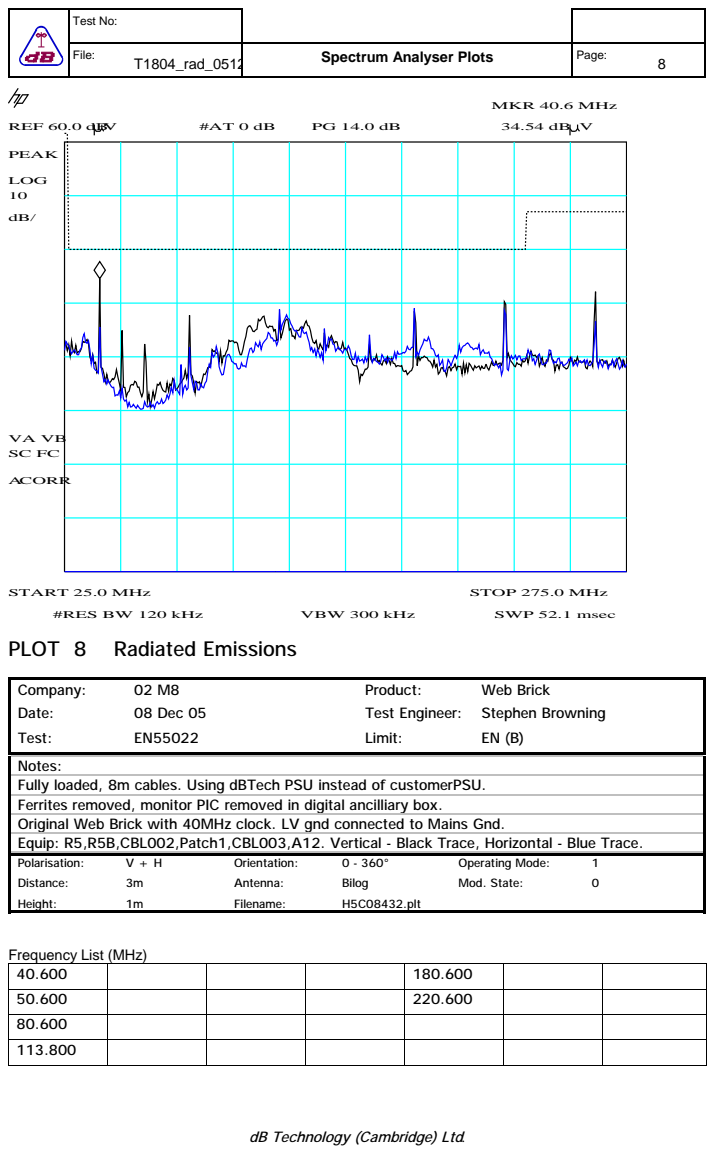
[picture p110: page 8]
#RES BW 120 kHz; VBW 300 kHz; SWP 52.1 msec; REF 60.0 dBV; LOG 10; START 25.0 MHz; STOP 275.0 MHz; MKR 40.6 MHz; PEAK; ACORR; Test:; Limit:; Date:; 08 Dec 05; Test Engineer: Stephen Browning; Company:; Product:; Web Brick; Height:; Filename:; H5C08432.plt; Distance:; Antenna:; Bilog; Mod. State:; Polarisation:; Orientation:; Operating Mode:

PLOT 8 Radiated Emissions

Notes:
Fully loaded, 8m cables. Using dBTech PSU instead of customerPSU.
Ferrites removed, monitor PIC removed in digital ancilliary box.
Original Web Brick with 40MHz clock. LV gnd connected to Mains Gnd.
Equip: R5,R5B,CBL002,Patch1,CBL003,A12. Vertical - Black Trace, Horizontal - Blue Trace.

Frequency List (MHz)

40.600 180.600
50.600 220.600
80.600
113.800

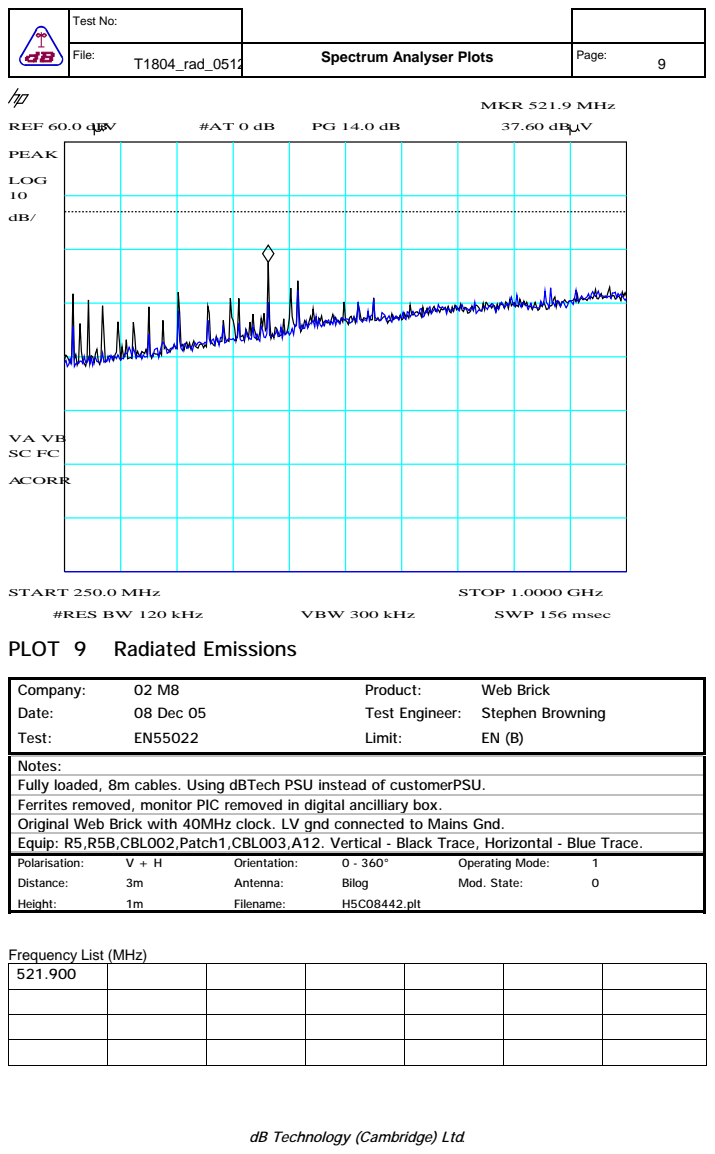
[picture p111: page 9]
#RES BW 120 kHz; VBW 300 kHz; SWP 156 msec; REF 60.0 dBV; LOG 10; START 250.0 MHz; STOP 1.0000 GHz; MKR 521.9 MHz; PEAK; ACORR; Test:; Limit:; Date:; 08 Dec 05; Test Engineer: Stephen Browning; Company:; Product:; Web Brick; Height:; Filename:; H5C08442.plt; Distance:; Antenna:; Bilog; Mod. State:; Polarisation:; Orientation:; Operating Mode:

PLOT 9 Radiated Emissions

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

Frequency List (MHz)
