LawrenceK/webbrick/Documentation/CETesting/T1804_con_051208.pdf

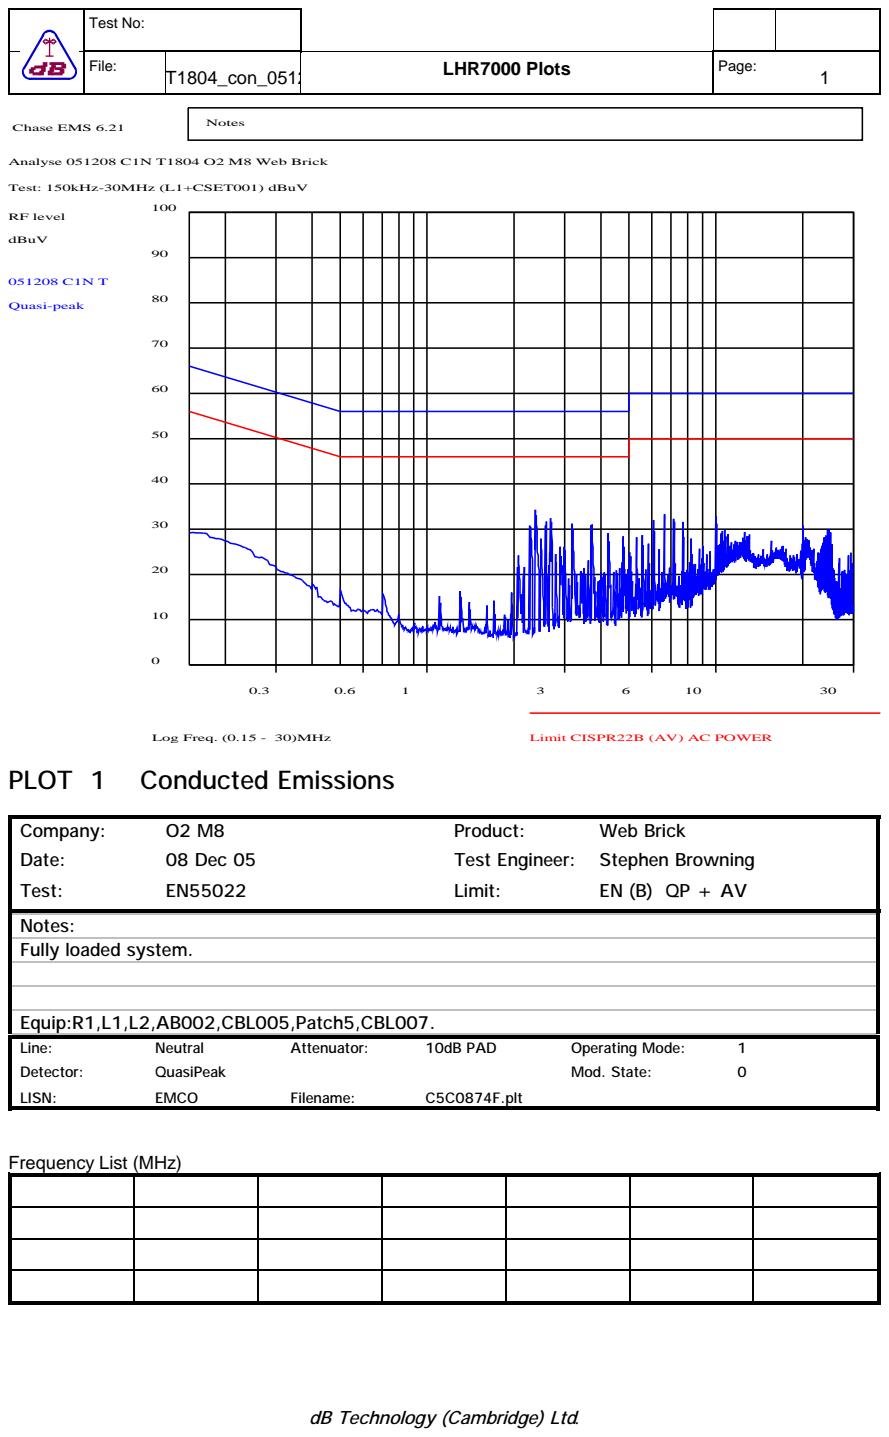
[picture p112: page 1]
Chase EMS 6.21; Notes; Test: 150kHz-30MHz (L1+CSET001) dBuV; RF level; dBuV; Quasi-peak; Test:; Limit:; Date:; 08 Dec 05; Test Engineer: Stephen Browning; Company:; Product:; Web Brick; Equip:R1,L1,L2,AB002,CBL005,Patch5,CBL007.; LISN:; EMCO; Filename:; C5C0874F.plt; Detector:; QuasiPeak; Mod. State:; Line:; Neutral; Attenuator:; 10dB PAD; Operating Mode:

Test No:

File: | LHR7000 Plots | Page: T1804_con_051208.l

Analyse 051208 C1N T1804 O2 M8 Web Brick

Log Freq. (0.15 - 30)MHz

Limit CISPR22B (AV) AC POWER

PLOT 1 Conducted Emissions

Notes:
Fully loaded system.

Frequency List (MHz)

dB Technology (Cambridge) Ltd.

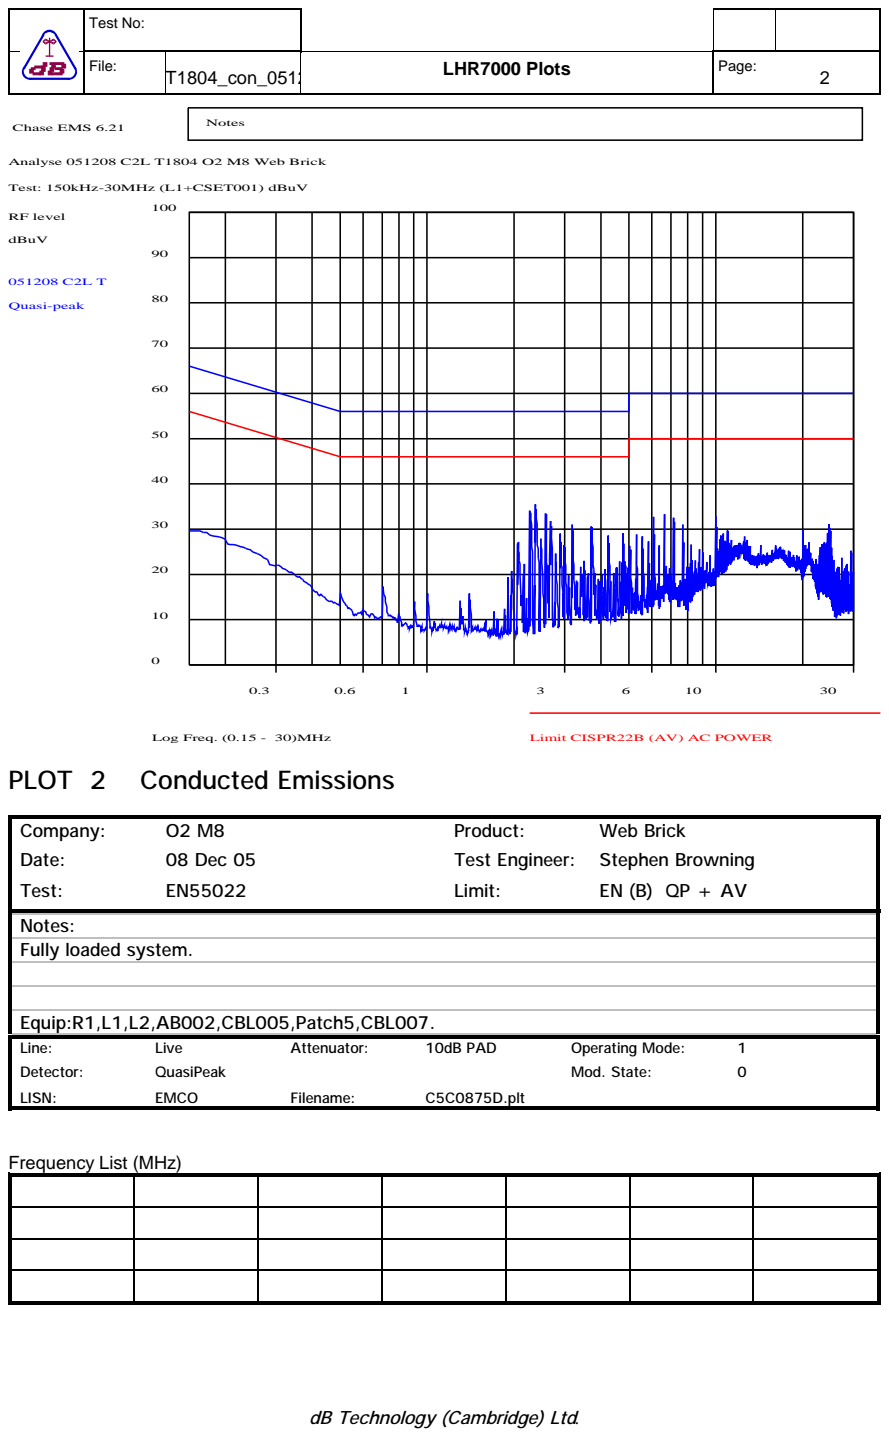
[picture p113: page 2]
Chase EMS 6.21; Notes; Test: 150kHz-30MHz (L1+CSET001) dBuV; RF level; dBuV; Quasi-peak; Test:; Limit:; Date:; 08 Dec 05; Test Engineer: Stephen Browning; Company:; Product:; Web Brick; Equip:R1,L1,L2,AB002,CBL005,Patch5,CBL007.; LISN:; EMCO; Filename:; C5C0875D.plt; Detector:; QuasiPeak; Mod. State:; Line:; Live; Attenuator:; 10dB PAD; Operating Mode:

Analyse 051208 C2L T1804 O2 M8 Web Brick

Log Freq. (0.15 - 30)MHz

Limit CISPR22B (AV) AC POWER

PLOT 2 Conducted Emissions

Notes:
Fully loaded system.

Frequency List (MHz)

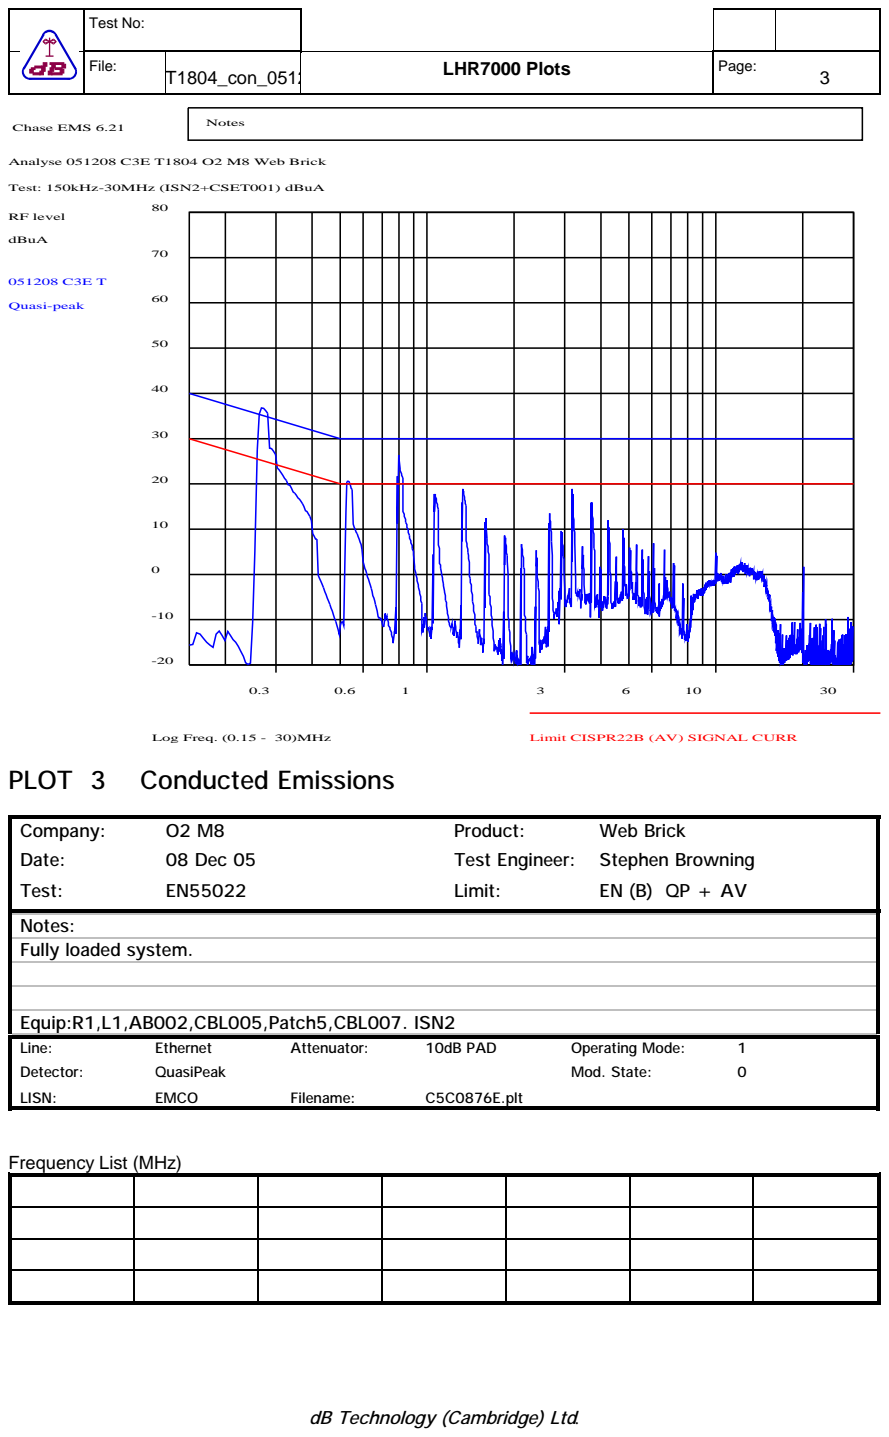
[picture p114: page 3]
Chase EMS 6.21; Notes; Test: 150kHz-30MHz (ISN2+CSET001) dBuA; RF level; dBuA; Quasi-peak; Test:; Limit:; Date:; 08 Dec 05; Test Engineer: Stephen Browning; Company:; Product:; Web Brick; Equip:R1,L1,AB002,CBL005,Patch5,CBL007. ISN2; LISN:; EMCO; Filename:; C5C0876E.plt; Detector:; QuasiPeak; Mod. State:; Line:; Ethernet; Attenuator:; 10dB PAD; Operating Mode:

Analyse 051208 C3E T1804 O2 M8 Web Brick

Log Freq. (0.15 - 30)MHz

Limit CISPR22B (AV) SIGNAL CURR

PLOT 3 Conducted Emissions

Notes:
Fully loaded system.

Frequency List (MHz)

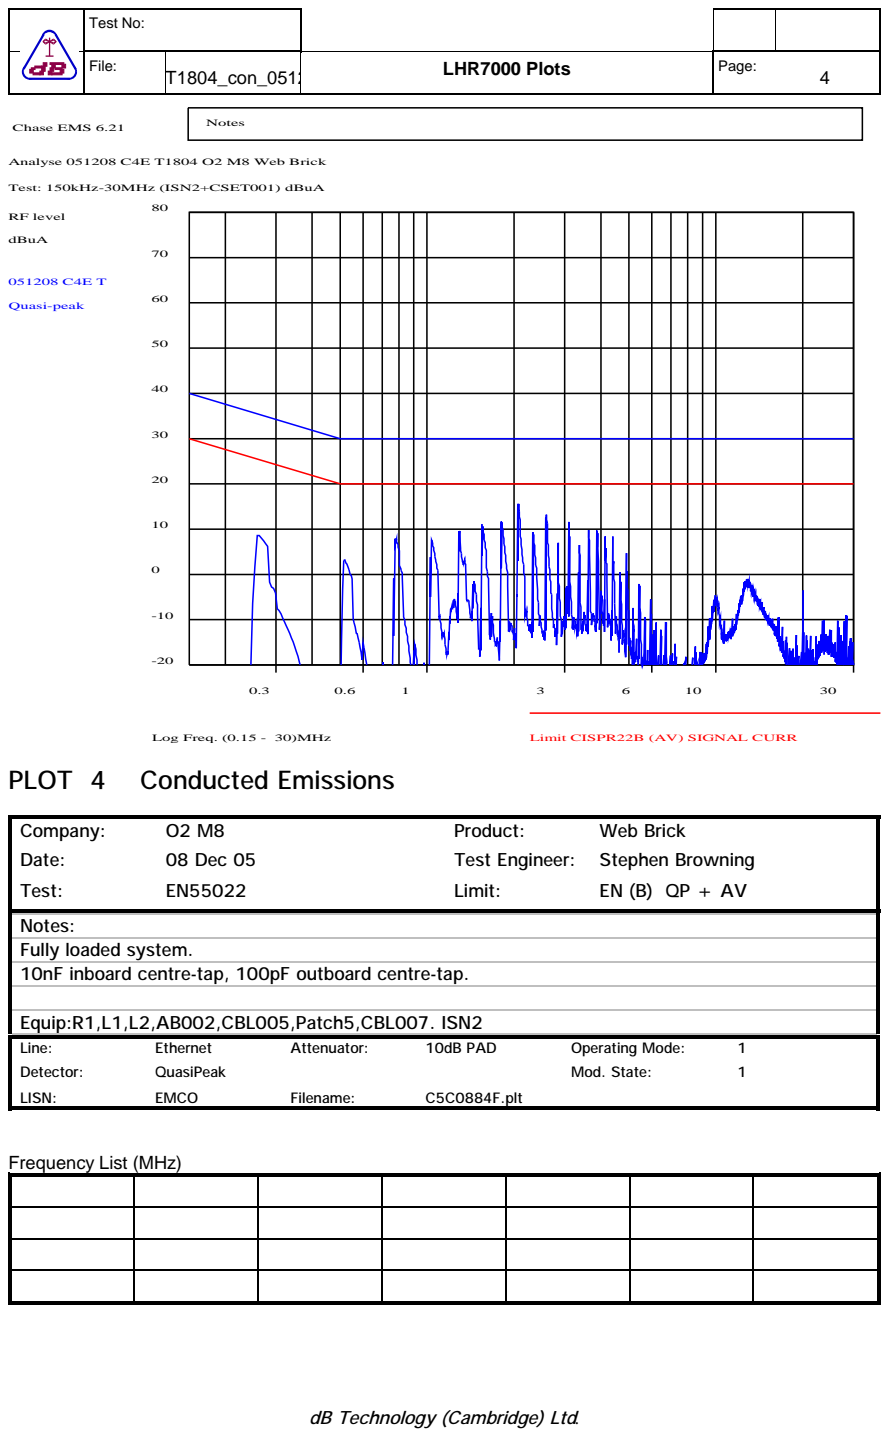
[picture p115: page 4]
Chase EMS 6.21; Notes; Test: 150kHz-30MHz (ISN2+CSET001) dBuA; RF level; dBuA; Quasi-peak; Test:; Limit:; Date:; 08 Dec 05; Test Engineer: Stephen Browning; Company:; Product:; Web Brick; Equip:R1,L1,L2,AB002,CBL005,Patch5,CBL007. ISN2; LISN:; EMCO; Filename:; C5C0884F.plt; Detector:; QuasiPeak; Mod. State:; Line:; Ethernet; Attenuator:; 10dB PAD; Operating Mode:

Analyse 051208 C4E T1804 O2 M8 Web Brick

Log Freq. (0.15 - 30)MHz

Limit CISPR22B (AV) SIGNAL CURR

PLOT 4 Conducted Emissions

Notes:
Fully loaded system.
10nF inboard centre-tap, 100pF outboard centre-tap.

Frequency List (MHz)
