LawrenceK/webbrick/Hardware/WebBrick/6.0/Top Artwork/OldArtwork/WebBrick6-0-64OverlaY.pdf

152.00

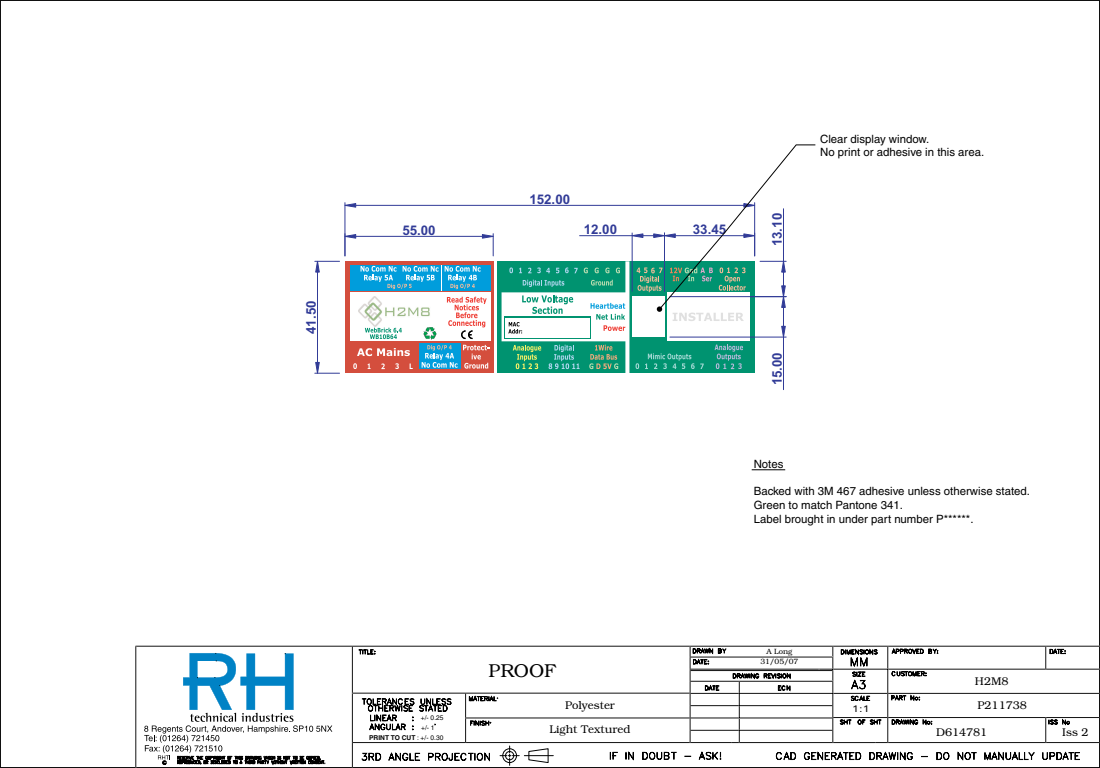
[picture p116: page 1]
Notes; A Long 31/05/07; PROOF; Iss 2; Polyester; Light Textured

Clear display window.
No print or adhesive in this area.

Backed with 3M 467 adhesive unless otherwise stated.
Green to match Pantone 341.
Label brought in under part number P******.

PRINT TO CUT : +/- 0.30
