LawrenceK/webbrick/Hardware/RTI/Firmware/Pt1000-08a.asm

	list p=12f683
	#include <p12f683.inc>
	radix dec
; Begin
	R0L EQU 0x20
	R0H EQU 0x21
	R1L EQU 0x22
	R1H EQU 0x23
	R2L EQU 0x24
	R2H EQU 0x25
	R3L EQU 0x26
	R3H EQU 0x27
	R4L EQU 0x28
	R4H EQU 0x29
	R5L EQU 0x2A
	R5H EQU 0x2B
	ORG 0x0000
	BCF PCLATH,3
	BCF PCLATH,4
	GOTO L0003
	ORG 0x0004
	RETFIE
L0003:
; 1: Define CONF_WORD = 0x3314
; 2: 
; 3: 
; 4: 
; 5: 
; 6: 
; 7: 
; 8: Define CLOCK_FREQUENCY = 4
; 9: 
; 10: TRISIO.1 = 1
	BSF STATUS,RP0
	BSF 0x05,1
; 11: TRISIO.2 = 0
	BCF 0x05,2
; 12: TRISIO.5 = 0
	BCF 0x05,5
; 13: 
; 14: Define ADC_CLOCK = 3
; 15: Define ADC_SAMPLEUS = 50
; 16: AllDigital
	CLRF 0x1F
	BCF STATUS,RP0
	MOVLW 0x07
	MOVWF 0x19
; 17: Dim sig As Word
;       The address of 'sig' is 0x2C
	sig EQU 0x2C
; 18: Dim pta As Word
;       The address of 'pta' is 0x2E
	pta EQU 0x2E
; 19: Dim i As Byte
;       The address of 'i' is 0x30
	i EQU 0x30
; 20: Dim l As Byte
;       The address of 'l' is 0x31
	l EQU 0x31
; 21: Dim p As Byte
;       The address of 'p' is 0x32
	p EQU 0x32
; 22: Dim pt As Word
;       The address of 'pt' is 0x33
	pt EQU 0x33
; 23: 
; 24:  'ADCON0 = %1100000
; 25: ANSEL = 8
	BSF STATUS,RP0
	MOVLW 0x08
	MOVWF 0x1F
; 26: 
	BCF STATUS,RP0
; 27: PWMon 1, 9
	MOVLW 0x3F
	BSF STATUS,RP0
	MOVWF PR2
	BCF TRISIO,2
	BCF STATUS,RP0
	CLRF CCPR1L
	BCF CCP1CON,DC1B1
	BCF CCP1CON,DC1B0
	BCF T2CON,T2CKPS0
	BCF T2CON,T2CKPS1
	BSF T2CON,TMR2ON
	MOVLW 0x0C
	IORWF CCP1CON,F
; 28: Gosub eefill
	CALL L0002
; 29: 
; 30: OPTION_REG = %10001111
	BSF STATUS,RP0
	MOVLW 0x8F
	MOVWF 0x01
	BCF STATUS,RP0
; 31: start: 
L0001:
; 32: ASM:        clrwdt
	       clrwdt
; 33: pta = 0
	CLRF 0x2E
	CLRF 0x2F
; 34: GPIO.5 = 0
	BCF 0x05,5
; 35: WaitMs 10
	MOVLW 0x0A
	MOVWF R0L
	CLRF R0H
	CALL W001
; 36: ASM:        clrwdt
	       clrwdt
; 37: For l = 0 To 7
	CLRF 0x31
L0004:
	MOVF 0x31,W
	SUBLW 0x07
	BTFSS STATUS,C
	GOTO L0005
; 38: Adcin 3, pt
	BSF ADCON0,ADFM
	BSF STATUS,RP0
	MOVLW 0x30
	IORWF ANSEL,F
	MOVLW 0x03
	BCF STATUS,RP0
	MOVWF R0L
	CALL A001
	BSF STATUS,RP0
	MOVF ADRESL,W
	BCF STATUS,RP0
	MOVWF 0x33
	MOVF ADRESH,W
	MOVWF 0x34
; 39: pta = pta + pt
	MOVF 0x2E,W
	ADDWF 0x33,W
	MOVWF 0x2E
	MOVF 0x2F,W
	BTFSC STATUS,C
	ADDLW 0x01
	ADDWF 0x34,W
	MOVWF 0x2F
; 40: Next l
	MOVLW 0x01
	ADDWF 0x31,F
	BTFSS STATUS,C
	GOTO L0004
L0005:	MOVLW 0x1F
	ANDWF STATUS,F
; 41: GPIO.5 = 1
	BSF 0x05,5
; 42: pt = pta / 8
	MOVF 0x2E,W
	MOVWF R0L
	MOVF 0x2F,W
	MOVWF R0H
	MOVLW 0x08
	MOVWF R1L
	CLRF R1H
	CALL D001
	MOVWF 0x33
	MOVF R0H,W
	MOVWF 0x34
; 43: If pt < 456 Then pt = 456
	MOVF 0x33,W
	MOVWF R0L
	MOVF 0x34,W
	MOVWF R0H
	MOVLW 0x01
	MOVWF R1H
	MOVLW 0xC8
	CALL C004
	BTFSS STATUS,Z
	GOTO L0006
	MOVLW 0xC8
	MOVWF 0x33
	MOVLW 0x01
	MOVWF 0x34
L0006:	MOVLW 0x1F
	ANDWF STATUS,F
; 44: If pt > 651 Then pt = 651
	MOVF 0x33,W
	MOVWF R0L
	MOVF 0x34,W
	MOVWF R0H
	MOVLW 0x02
	MOVWF R1H
	MOVLW 0x8B
	CALL C003
	BTFSS STATUS,Z
	GOTO L0007
	MOVLW 0x8B
	MOVWF 0x33
	MOVLW 0x02
	MOVWF 0x34
L0007:	MOVLW 0x1F
	ANDWF STATUS,F
; 45: p = pt - 456 '(0 To 196)
;       The address of 'oshonsoft_temp_1' is 0x35
	oshonsoft_temp_1 EQU 0x35
	MOVLW 0xC8
	SUBWF 0x33,W
	MOVWF 0x35
	MOVLW 0x01
	BTFSS STATUS,C
	ADDLW 0x01
	SUBWF 0x34,W
	MOVWF 0x36
	MOVF 0x35,W
	MOVWF 0x32
; 46: Read p, i
	MOVF 0x32,W
	BSF STATUS,RP0
	MOVWF EEADR
	BSF EECON1,RD
	NOP
	MOVF EEDATA,W
	BCF STATUS,RP0
	MOVWF 0x30
; 47: PWMduty 1, i
	MOVF 0x30,W
	MOVWF R0L
	BTFSC R0L,0
	BSF CCP1CON,DC1B0
	BTFSS R0L,0
	BCF CCP1CON,DC1B0
	BTFSC R0L,1
	BSF CCP1CON,DC1B1
	BTFSS R0L,1
	BCF CCP1CON,DC1B1
	BCF STATUS,C
	RRF R0L,F
	BCF STATUS,C
	RRF R0L,W
	MOVWF CCPR1L
; 48: ASM:        clrwdt
	       clrwdt
; 49: WaitMs 255
	MOVLW 0xFF
	MOVWF R0L
	CLRF R0H
	CALL W001
; 50: ASM:        clrwdt
	       clrwdt
; 51: Goto start
	GOTO L0001
; 52: End
L0008:	GOTO L0008
; 53: eefill: 
L0002:
; 54: EEPROM 0, 0
; 55: EEPROM 1, 1
; 56: EEPROM 2, 2
; 57: EEPROM 3, 3
; 58: EEPROM 4, 4
; 59: EEPROM 5, 4
; 60: EEPROM 6, 5
; 61: EEPROM 7, 6
; 62: EEPROM 8, 7
; 63: EEPROM 9, 8
; 64: EEPROM 10, 8
; 65: EEPROM 11, 9
; 66: EEPROM 12, 10
; 67: EEPROM 13, 11
; 68: EEPROM 14, 12
; 69: EEPROM 15, 13
; 70: EEPROM 16, 13
; 71: EEPROM 17, 14
; 72: EEPROM 18, 15
; 73: EEPROM 19, 16
; 74: EEPROM 20, 17
; 75: EEPROM 21, 18
; 76: EEPROM 22, 19
; 77: EEPROM 23, 20
; 78: EEPROM 24, 20
; 79: EEPROM 25, 21
; 80: EEPROM 26, 22
; 81: EEPROM 27, 23
; 82: EEPROM 28, 24
; 83: EEPROM 29, 26
; 84: EEPROM 30, 27
; 85: EEPROM 31, 28
; 86: EEPROM 32, 29
; 87: EEPROM 33, 29
; 88: EEPROM 34, 30
; 89: EEPROM 35, 31
; 90: EEPROM 36, 32
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
	DW 0xC6
	DW 0xC8
	DW 0xCA
	DW 0xCB
	DW 0xCD
	DW 0xCF
	DW 0xD1
	DW 0xD2
	DW 0xD4
	DW 0xD6
	DW 0xD8
	DW 0xDA
	DW 0xDB
	DW 0xDD
	DW 0xDF
	DW 0xE1
	DW 0xE3
	DW 0xE6
	DW 0xE7
	DW 0xE9
	DW 0xEB
	DW 0xED
	DW 0xEF
	DW 0xF1
	DW 0xF3
	DW 0xF5
	DW 0xF7
	DW 0xF9
	DW 0xFB
	DW 0xFD
; End of listing
	END
