LawrenceK/webbrick/PIC/Parse.h

//
//  Copyright L.P.Klyne 2013
//
//  Filename: Parse.h
//
//  Description: Contains all code for parsing incomming commands
//
//  Notes:
//
//
// Include files

//#include "template.h"

// Defines

// Static data (Global scope)

// Exported functions declarations
void CheckForCmds();    // Check the siteplayer for inbound commands.
// Flush the serial input buffer
void FlushCmds();
