LawrenceK/webbrick/PIC/errors.h

//
//  Copyright L.P.Klyne 2013
//
//  Filename: errors.h
//
//  Description:    error values
//
//  Notes:
//
//
// Include files

#define ERR_None  0
#define ERR_BadCommand  1
#define ERR_BadParam    2
#define ERR_NotLoggedIn    3
#define ERR_AddressLocked   4
#define ERR_Startup   5
#define ERR_NoCommand   6
