LawrenceK/webbrick/PIC/version_base.h

//
//  Copyright L.P.Klyne 2013
//
//  Filename: version.h
//
//  Description:    software version number
//
//  Notes:
//
//
// Include files
#define DF_SW_VER_MAJOR   6
#define DF_SW_VER_MINOR   7
#define DF_SW_VER_BUILD   0
